ashgang/morphy/Software/ReferenceApplication/pca10056/s140/config/sdk_config.h

/**
 * Copyright (c) 2017 - 2020, Nordic Semiconductor ASA
 *
 * All rights reserved.
 *
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
 * 3. Neither the name of Nordic Semiconductor ASA nor the names of its
 *    contributors may be used to endorse or promote products derived from this
 *    software without specific prior written permission.
 *
 * 4. This software, with or without modification, must only be used with a
 *    Nordic Semiconductor ASA integrated circuit.
 *
 * 5. Any software provided in binary form under this license must not be reverse
 *    engineered, decompiled, modified and/or disassembled.
 *
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
 */



#ifndef SDK_CONFIG_H
#define SDK_CONFIG_H
// <<< Use Configuration Wizard in Context Menu >>>\n
#ifdef USE_APP_CONFIG
#include "app_config.h"
#endif
// <h> Board Support 

//==========================================================
// <q> BSP_BTN_BLE_ENABLED  - bsp_btn_ble - Button Control for BLE
 

#ifndef BSP_BTN_BLE_ENABLED
#define BSP_BTN_BLE_ENABLED 1
#endif

// </h> 
//==========================================================

// <h> nRF_BLE 

//==========================================================
// <q> BLE_ADVERTISING_ENABLED  - ble_advertising - Advertising module
 

#ifndef BLE_ADVERTISING_ENABLED
#define BLE_ADVERTISING_ENABLED 1
#endif

// <e> BLE_DTM_ENABLED - ble_dtm - Module for testing RF/PHY using DTM commands
//==========================================================
#ifndef BLE_DTM_ENABLED
#define BLE_DTM_ENABLED 0
#endif
// <o> NRF_RADIO_ANTENNA_PIN_1 - Antenna 1 GPIO pin 
#ifndef NRF_RADIO_ANTENNA_PIN_1
#define NRF_RADIO_ANTENNA_PIN_1 21
#endif

// <o> NRF_RADIO_ANTENNA_PIN_2 - Antenna 2 GPIO pin 
#ifndef NRF_RADIO_ANTENNA_PIN_2
#define NRF_RADIO_ANTENNA_PIN_2 23
#endif

// <o> NRF_RADIO_ANTENNA_PIN_3 - Antenna 3 GPIO pin 
#ifndef NRF_RADIO_ANTENNA_PIN_3
#define NRF_RADIO_ANTENNA_PIN_3 26
#endif

// <o> NRF_RADIO_ANTENNA_PIN_4 - Antenna 4 GPIO pin 
#ifndef NRF_RADIO_ANTENNA_PIN_4
#define NRF_RADIO_ANTENNA_PIN_4 27
#endif

// <o> NRF_RADIO_ANTENNA_PIN_5 - Antenna 5 GPIO pin 
#ifndef NRF_RADIO_ANTENNA_PIN_5
#define NRF_RADIO_ANTENNA_PIN_5 28
#endif

// <o> NRF_RADIO_ANTENNA_PIN_6 - Antenna 6 GPIO pin 
#ifndef NRF_RADIO_ANTENNA_PIN_6
#define NRF_RADIO_ANTENNA_PIN_6 29
#endif

// <o> NRF_RADIO_ANTENNA_PIN_7 - Antenna 7 GPIO pin 
#ifndef NRF_RADIO_ANTENNA_PIN_7
#define NRF_RADIO_ANTENNA_PIN_7 30
#endif

// <o> NRF_RADIO_ANTENNA_PIN_8 - Antenna 8 GPIO pin 
#ifndef NRF_RADIO_ANTENNA_PIN_8
#define NRF_RADIO_ANTENNA_PIN_8 31
#endif

// <o> NRF_RADIO_ANTENNA_COUNT  
#ifndef NRF_RADIO_ANTENNA_COUNT
#define NRF_RADIO_ANTENNA_COUNT 12
#endif

// </e>

// <q> BLE_RACP_ENABLED  - ble_racp - Record Access Control Point library
 

#ifndef BLE_RACP_ENABLED
#define BLE_RACP_ENABLED 0
#endif

// <e> NRF_BLE_CONN_PARAMS_ENABLED - ble_conn_params - Initiating and executing a connection parameters negotiation procedure
//==========================================================
#ifndef NRF_BLE_CONN_PARAMS_ENABLED
#define NRF_BLE_CONN_PARAMS_ENABLED 1
#endif
// <o> NRF_BLE_CONN_PARAMS_MAX_SLAVE_LATENCY_DEVIATION - The largest acceptable deviation in slave latency. 
// <i> The largest deviation (+ or -) from the requested slave latency that will not be renegotiated.

#ifndef NRF_BLE_CONN_PARAMS_MAX_SLAVE_LATENCY_DEVIATION
#define NRF_BLE_CONN_PARAMS_MAX_SLAVE_LATENCY_DEVIATION 499
#endif

// <o> NRF_BLE_CONN_PARAMS_MAX_SUPERVISION_TIMEOUT_DEVIATION - The largest acceptable deviation (in 10 ms units) in supervision timeout. 
// <i> The largest deviation (+ or -, in 10 ms units) from the requested supervision timeout that will not be renegotiated.

#ifndef NRF_BLE_CONN_PARAMS_MAX_SUPERVISION_TIMEOUT_DEVIATION
#define NRF_BLE_CONN_PARAMS_MAX_SUPERVISION_TIMEOUT_DEVIATION 65535
#endif

// </e>

// <q> NRF_BLE_GATT_ENABLED  - nrf_ble_gatt - GATT module
 

#ifndef NRF_BLE_GATT_ENABLED
#define NRF_BLE_GATT_ENABLED 1
#endif

// <e> NRF_BLE_QWR_ENABLED - nrf_ble_qwr - Queued writes support module (prepare/execute write)
//==========================================================
#ifndef NRF_BLE_QWR_ENABLED
#define NRF_BLE_QWR_ENABLED 1
#endif
// <o> NRF_BLE_QWR_MAX_ATTR - Maximum number of attribute handles that can be registered. This number must be adjusted according to the number of attributes for which Queued Writes will be enabled. If it is zero, the module will reject all Queued Write requests. 
#ifndef NRF_BLE_QWR_MAX_ATTR
#define NRF_BLE_QWR_MAX_ATTR 0
#endif

// </e>

// <e> PEER_MANAGER_ENABLED - peer_manager - Peer Manager
//==========================================================
#ifndef PEER_MANAGER_ENABLED
#define PEER_MANAGER_ENABLED 1
#endif
// <o> PM_MAX_REGISTRANTS - Number of event handlers that can be registered. 
#ifndef PM_MAX_REGISTRANTS
#define PM_MAX_REGISTRANTS 3
#endif

// <o> PM_FLASH_BUFFERS - Number of internal buffers for flash operations. 
// <i> Decrease this value to lower RAM usage.

#ifndef PM_FLASH_BUFFERS
#define PM_FLASH_BUFFERS 4
#endif

// <q> PM_CENTRAL_ENABLED  - Enable/disable central-specific Peer Manager functionality.
 

// <i> Enable/disable central-specific Peer Manager functionality.

#ifndef PM_CENTRAL_ENABLED
#define PM_CENTRAL_ENABLED 0
#endif

// <q> PM_SERVICE_CHANGED_ENABLED  - Enable/disable the service changed management for GATT server in Peer Manager.
 

// <i> If not using a GATT server, or using a server wihout a service changed characteristic,
// <i> disable this to save code space.

#ifndef PM_SERVICE_CHANGED_ENABLED
#define PM_SERVICE_CHANGED_ENABLED 1
#endif

// <q> PM_PEER_RANKS_ENABLED  - Enable/disable the peer rank management in Peer Manager.
 

// <i> Set this to false to save code space if not using the peer rank API.

#ifndef PM_PEER_RANKS_ENABLED
#define PM_PEER_RANKS_ENABLED 1
#endif

// <q> PM_LESC_ENABLED  - Enable/disable LESC support in Peer Manager.
 

// <i> If set to true, you need to call nrf_ble_lesc_request_handler() in the main loop to respond to LESC-related BLE events. If LESC support is not required, set this to false to save code space.

#ifndef PM_LESC_ENABLED
#define PM_LESC_ENABLED 0
#endif

// <e> PM_RA_PROTECTION_ENABLED - Enable/disable protection against repeated pairing attempts in Peer Manager.
//==========================================================
#ifndef PM_RA_PROTECTION_ENABLED
#define PM_RA_PROTECTION_ENABLED 0
#endif
// <o> PM_RA_PROTECTION_TRACKED_PEERS_NUM - Maximum number of peers whose authorization status can be tracked. 
#ifndef PM_RA_PROTECTION_TRACKED_PEERS_NUM
#define PM_RA_PROTECTION_TRACKED_PEERS_NUM 8
#endif

// <o> PM_RA_PROTECTION_MIN_WAIT_INTERVAL - Minimum waiting interval (in ms) before a new pairing attempt can be initiated. 
#ifndef PM_RA_PROTECTION_MIN_WAIT_INTERVAL
#define PM_RA_PROTECTION_MIN_WAIT_INTERVAL 4000
#endif

// <o> PM_RA_PROTECTION_MAX_WAIT_INTERVAL - Maximum waiting interval (in ms) before a new pairing attempt can be initiated. 
#ifndef PM_RA_PROTECTION_MAX_WAIT_INTERVAL
#define PM_RA_PROTECTION_MAX_WAIT_INTERVAL 64000
#endif

// <o> PM_RA_PROTECTION_REWARD_PERIOD - Reward period (in ms). 
// <i> The waiting interval is gradually decreased when no new failed pairing attempts are made during reward period.

#ifndef PM_RA_PROTECTION_REWARD_PERIOD
#define PM_RA_PROTECTION_REWARD_PERIOD 10000
#endif

// </e>

// <o> PM_HANDLER_SEC_DELAY_MS - Delay before starting security. 
// <i>  This might be necessary for interoperability reasons, especially as peripheral.

#ifndef PM_HANDLER_SEC_DELAY_MS
#define PM_HANDLER_SEC_DELAY_MS 0
#endif

// </e>

// </h> 
//==========================================================

// <h> nRF_BLE_Services 

//==========================================================
// <q> BLE_ANCS_C_ENABLED  - ble_ancs_c - Apple Notification Service Client
 

#ifndef BLE_ANCS_C_ENABLED
#define BLE_ANCS_C_ENABLED 0
#endif

// <q> BLE_ANS_C_ENABLED  - ble_ans_c - Alert Notification Service Client
 

#ifndef BLE_ANS_C_ENABLED
#define BLE_ANS_C_ENABLED 0
#endif

// <q> BLE_BAS_C_ENABLED  - ble_bas_c - Battery Service Client
 

#ifndef BLE_BAS_C_ENABLED
#define BLE_BAS_C_ENABLED 0
#endif

// <e> BLE_BAS_ENABLED - ble_bas - Battery Service
//==========================================================
#ifndef BLE_BAS_ENABLED
#define BLE_BAS_ENABLED 1
#endif
// <e> BLE_BAS_CONFIG_LOG_ENABLED - Enables logging in the module.
//==========================================================
#ifndef BLE_BAS_CONFIG_LOG_ENABLED
#define BLE_BAS_CONFIG_LOG_ENABLED 0
#endif
// <o> BLE_BAS_CONFIG_LOG_LEVEL  - Default Severity level
 
// <0=> Off 
// <1=> Error 
// <2=> Warning 
// <3=> Info 
// <4=> Debug 

#ifndef BLE_BAS_CONFIG_LOG_LEVEL
#define BLE_BAS_CONFIG_LOG_LEVEL 3
#endif

// <o> BLE_BAS_CONFIG_INFO_COLOR  - ANSI escape code prefix.
 
// <0=> Default 
// <1=> Black 
// <2=> Red 
// <3=> Green 
// <4=> Yellow 
// <5=> Blue 
// <6=> Magenta 
// <7=> Cyan 
// <8=> White 

#ifndef BLE_BAS_CONFIG_INFO_COLOR
#define BLE_BAS_CONFIG_INFO_COLOR 0
#endif

// <o> BLE_BAS_CONFIG_DEBUG_COLOR  - ANSI escape code prefix.
 
// <0=> Default 
// <1=> Black 
// <2=> Red 
// <3=> Green 
// <4=> Yellow 
// <5=> Blue 
// <6=> Magenta 
// <7=> Cyan 
// <8=> White 

#ifndef BLE_BAS_CONFIG_DEBUG_COLOR
#define BLE_BAS_CONFIG_DEBUG_COLOR 0
#endif

// </e>

// </e>

// <q> BLE_CSCS_ENABLED  - ble_cscs - Cycling Speed and Cadence Service
 

#ifndef BLE_CSCS_ENABLED
#define BLE_CSCS_ENABLED 0
#endif

// <q> BLE_CTS_C_ENABLED  - ble_cts_c - Current Time Service Client
 

#ifndef BLE_CTS_C_ENABLED
#define BLE_CTS_C_ENABLED 0
#endif

// <q> BLE_DIS_ENABLED  - ble_dis - Device Information Service
 

#ifndef BLE_DIS_ENABLED
#define BLE_DIS_ENABLED 1
#endif

// <q> BLE_GLS_ENABLED  - ble_gls - Glucose Service
 

#ifndef BLE_GLS_ENABLED
#define BLE_GLS_ENABLED 0
#endif

// <q> BLE_HIDS_ENABLED  - ble_hids - Human Interface Device Service
 

#ifndef BLE_HIDS_ENABLED
#define BLE_HIDS_ENABLED 0
#endif

// <q> BLE_HRS_C_ENABLED  - ble_hrs_c - Heart Rate Service Client
 

#ifndef BLE_HRS_C_ENABLED
#define BLE_HRS_C_ENABLED 0
#endif

// <q> BLE_HRS_ENABLED  - ble_hrs - Heart Rate Service
 

#ifndef BLE_HRS_ENABLED
#define BLE_HRS_ENABLED 1
#endif

// <q> BLE_HTS_ENABLED  - ble_hts - Health Thermometer Service
 

#ifndef BLE_HTS_ENABLED
#define BLE_HTS_ENABLED 0
#endif

// <q> BLE_IAS_C_ENABLED  - ble_ias_c - Immediate Alert Service Client
 

#ifndef BLE_IAS_C_ENABLED
#define BLE_IAS_C_ENABLED 0
#endif

// <e> BLE_IAS_ENABLED - ble_ias - Immediate Alert Service
//==========================================================
#ifndef BLE_IAS_ENABLED
#define BLE_IAS_ENABLED 0
#endif
// <e> BLE_IAS_CONFIG_LOG_ENABLED - Enables logging in the module.
//==========================================================
#ifndef BLE_IAS_CONFIG_LOG_ENABLED
#define BLE_IAS_CONFIG_LOG_ENABLED 0
#endif
// <o> BLE_IAS_CONFIG_LOG_LEVEL  - Default Severity level
 
// <0=> Off 
// <1=> Error 
// <2=> Warning 
// <3=> Info 
// <4=> Debug 

#ifndef BLE_IAS_CONFIG_LOG_LEVEL
#define BLE_IAS_CONFIG_LOG_LEVEL 3
#endif

// <o> BLE_IAS_CONFIG_INFO_COLOR  - ANSI escape code prefix.
 
// <0=> Default 
// <1=> Black 
// <2=> Red 
// <3=> Green 
// <4=> Yellow 
// <5=> Blue 
// <6=> Magenta 
// <7=> Cyan 
// <8=> White 

#ifndef BLE_IAS_CONFIG_INFO_COLOR
#define BLE_IAS_CONFIG_INFO_COLOR 0
#endif

// <o> BLE_IAS_CONFIG_DEBUG_COLOR  - ANSI escape code prefix.
 
// <0=> Default 
// <1=> Black 
// <2=> Red 
// <3=> Green 
// <4=> Yellow 
// <5=> Blue 
// <6=> Magenta 
// <7=> Cyan 
// <8=> White 

#ifndef BLE_IAS_CONFIG_DEBUG_COLOR
#define BLE_IAS_CONFIG_DEBUG_COLOR 0
#endif

// </e>

// </e>

// <q> BLE_LBS_C_ENABLED  - ble_lbs_c - Nordic LED Button Service Client
 

#ifndef BLE_LBS_C_ENABLED
#define BLE_LBS_C_ENABLED 0
#endif

// <q> BLE_LBS_ENABLED  - ble_lbs - LED Button Service
 

#ifndef BLE_LBS_ENABLED
#define BLE_LBS_ENABLED 0
#endif

// <q> BLE_LLS_ENABLED  - ble_lls - Link Loss Service
 

#ifndef BLE_LLS_ENABLED
#define BLE_LLS_ENABLED 0
#endif

// <q> BLE_NUS_C_ENABLED  - ble_nus_c - Nordic UART Central Service
 

#ifndef BLE_NUS_C_ENABLED
#define BLE_NUS_C_ENABLED 0
#endif

// <e> BLE_NUS_ENABLED - ble_nus - Nordic UART Service
//==========================================================
#ifndef BLE_NUS_ENABLED
#define BLE_NUS_ENABLED 0
#endif
// <e> BLE_NUS_CONFIG_LOG_ENABLED - Enables logging in the module.
//==========================================================
#ifndef BLE_NUS_CONFIG_LOG_ENABLED
#define BLE_NUS_CONFIG_LOG_ENABLED 0
#endif
// <o> BLE_NUS_CONFIG_LOG_LEVEL  - Default Severity level
 
// <0=> Off 
// <1=> Error 
// <2=> Warning 
// <3=> Info 
// <4=> Debug 

#ifndef BLE_NUS_CONFIG_LOG_LEVEL
#define BLE_NUS_CONFIG_LOG_LEVEL 3
#endif

// <o> BLE_NUS_CONFIG_INFO_COLOR  - ANSI escape code prefix.
 
// <0=> Default 
// <1=> Black 
// <2=> Red 
// <3=> Green 
// <4=> Yellow 
// <5=> Blue 
// <6=> Magenta 
// <7=> Cyan 
// <8=> White 

#ifndef BLE_NUS_CONFIG_INFO_COLOR
#define BLE_NUS_CONFIG_INFO_COLOR 0
#endif

// <o> BLE_NUS_CONFIG_DEBUG_COLOR  - ANSI escape code prefix.
 
// <0=> Default 
// <1=> Black 
// <2=> Red 
// <3=> Green 
// <4=> Yellow 
// <5=> Blue 
// <6=> Magenta 
// <7=> Cyan 
// <8=> White 

#ifndef BLE_NUS_CONFIG_DEBUG_COLOR
#define BLE_NUS_CONFIG_DEBUG_COLOR 0
#endif

// </e>

// </e>

// <q> BLE_RSCS_C_ENABLED  - ble_rscs_c - Running Speed and Cadence Client
 

#ifndef BLE_RSCS_C_ENABLED
#define BLE_RSCS_C_ENABLED 0
#endif

// <q> BLE_RSCS_ENABLED  - ble_rscs - Running Speed and Cadence Service
 

#ifndef BLE_RSCS_ENABLED
#define BLE_RSCS_ENABLED 0
#endif

// <q> BLE_TPS_ENABLED  - ble_tps - TX Power Service
 

#ifndef BLE_TPS_ENABLED
#define BLE_TPS_ENABLED 0
#endif

// </h> 
//==========================================================

// <h> nRF_Core 

//==========================================================
// <e> NRF_MPU_LIB_ENABLED - nrf_mpu_lib - Module for MPU
//==========================================================
#ifndef NRF_MPU_LIB_ENABLED
#define NRF_MPU_LIB_ENABLED 0
#endif
// <q> NRF_MPU_LIB_CLI_CMDS  - Enable CLI commands specific to the module.
 

#ifndef NRF_MPU_LIB_CLI_CMDS
#define NRF_MPU_LIB_CLI_CMDS 0
#endif

// </e>

// <e> NRF_STACK_GUARD_ENABLED - nrf_stack_guard - Stack guard
//==========================================================
#ifndef NRF_STACK_GUARD_ENABLED
#define NRF_STACK_GUARD_ENABLED 0
#endif
// <o> NRF_STACK_GUARD_CONFIG_SIZE  - Size of the stack guard.
 
// <5=> 32 bytes 
// <6=> 64 bytes 
// <7=> 128 bytes 
// <8=> 256 bytes 
// <9=> 512 bytes 
// <10=> 1024 bytes 
// <11=> 2048 bytes 
// <12=> 4096 bytes 

#ifndef NRF_STACK_GUARD_CONFIG_SIZE
#define NRF_STACK_GUARD_CONFIG_SIZE 7
#endif

// </e>

// </h> 
//==========================================================

// <h> nRF_Crypto 

//==========================================================
// <e> NRF_CRYPTO_ENABLED - nrf_crypto - Cryptography library.
//==========================================================
#ifndef NRF_CRYPTO_ENABLED
#define NRF_CRYPTO_ENABLED 1
#endif
// <o> NRF_CRYPTO_ALLOCATOR  - Memory allocator
 

// <i> Choose memory allocator used by nrf_crypto. Default is alloca if possible or nrf_malloc otherwise. If 'User macros' are selected, the user has to create 'nrf_crypto_allocator.h' file that contains NRF_CRYPTO_ALLOC, NRF_CRYPTO_FREE, and NRF_CRYPTO_ALLOC_ON_STACK.
// <0=> Default 
// <1=> User macros 
// <2=> On stack (alloca) 
// <3=> C dynamic memory (malloc) 
// <4=> SDK Memory Manager (nrf_malloc) 

#ifndef NRF_CRYPTO_ALLOCATOR
#define NRF_CRYPTO_ALLOCATOR 0
#endif

// <e> NRF_CRYPTO_BACKEND_CC310_BL_ENABLED - Enable the ARM Cryptocell CC310 reduced backend.

// <i> The CC310 hardware-accelerated cryptography backend with reduced functionality and footprint (only available on nRF52840).
//==========================================================
#ifndef NRF_CRYPTO_BACKEND_CC310_BL_ENABLED
#define NRF_CRYPTO_BACKEND_CC310_BL_ENABLED 0
#endif
// <q> NRF_CRYPTO_BACKEND_CC310_BL_ECC_SECP224R1_ENABLED  - Enable the secp224r1 elliptic curve support using CC310_BL.
 

#ifndef NRF_CRYPTO_BACKEND_CC310_BL_ECC_SECP224R1_ENABLED
#define NRF_CRYPTO_BACKEND_CC310_BL_ECC_SECP224R1_ENABLED 0
#endif

// <q> NRF_CRYPTO_BACKEND_CC310_BL_ECC_SECP256R1_ENABLED  - Enable the secp256r1 elliptic curve support using CC310_BL.
 

#ifndef NRF_CRYPTO_BACKEND_CC310_BL_ECC_SECP256R1_ENABLED
#define NRF_CRYPTO_BACKEND_CC310_BL_ECC_SECP256R1_ENABLED 1
#endif

// <q> NRF_CRYPTO_BACKEND_CC310_BL_HASH_SHA256_ENABLED  - CC310_BL SHA-256 hash functionality.
 

// <i> CC310_BL backend implementation for hardware-accelerated SHA-256.

#ifndef NRF_CRYPTO_BACKEND_CC310_BL_HASH_SHA256_ENABLED
#define NRF_CRYPTO_BACKEND_CC310_BL_HASH_SHA256_ENABLED 1
#endif

// <q> NRF_CRYPTO_BACKEND_CC310_BL_HASH_AUTOMATIC_RAM_BUFFER_ENABLED  - nrf_cc310_bl buffers to RAM before running hash operation
 

// <i> Enabling this makes hashing of addresses in FLASH range possible. Size of buffer allocated for hashing is set by NRF_CRYPTO_BACKEND_CC310_BL_HASH_AUTOMATIC_RAM_BUFFER_SIZE

#ifndef NRF_CRYPTO_BACKEND_CC310_BL_HASH_AUTOMATIC_RAM_BUFFER_ENABLED
#define NRF_CRYPTO_BACKEND_CC310_BL_HASH_AUTOMATIC_RAM_BUFFER_ENABLED 0
#endif

// <o> NRF_CRYPTO_BACKEND_CC310_BL_HASH_AUTOMATIC_RAM_BUFFER_SIZE - nrf_cc310_bl hash outputs digests in little endian 
// <i> Makes the nrf_cc310_bl hash functions output digests in little endian format. Only for use in nRF SDK DFU!

#ifndef NRF_CRYPTO_BACKEND_CC310_BL_HASH_AUTOMATIC_RAM_BUFFER_SIZE
#define NRF_CRYPTO_BACKEND_CC310_BL_HASH_AUTOMATIC_RAM_BUFFER_SIZE 4096
#endif

// <q> NRF_CRYPTO_BACKEND_CC310_BL_INTERRUPTS_ENABLED  - Enable Interrupts while support using CC310 bl.
 

// <i> Select a library version compatible with the configuration. When interrupts are disable, a version named _noint must be used

#ifndef NRF_CRYPTO_BACKEND_CC310_BL_INTERRUPTS_ENABLED
#define NRF_CRYPTO_BACKEND_CC310_BL_INTERRUPTS_ENABLED 1
#endif

// </e>

// <e> NRF_CRYPTO_BACKEND_CC310_ENABLED - Enable the ARM Cryptocell CC310 backend.

// <i> The CC310 hardware-accelerated cryptography backend (only available on nRF52840).
//==========================================================
#ifndef NRF_CRYPTO_BACKEND_CC310_ENABLED
#define NRF_CRYPTO_BACKEND_CC310_ENABLED 0
#endif
// <q> NRF_CRYPTO_BACKEND_CC310_AES_CBC_ENABLED  - Enable the AES CBC mode using CC310.
 

#ifndef NRF_CRYPTO_BACKEND_CC310_AES_CBC_ENABLED
#define NRF_CRYPTO_BACKEND_CC310_AES_CBC_ENABLED 1
#endif

// <q> NRF_CRYPTO_BACKEND_CC310_AES_CTR_ENABLED  - Enable the AES CTR mode using CC310.
 

#ifndef NRF_CRYPTO_BACKEND_CC310_AES_CTR_ENABLED
#define NRF_CRYPTO_BACKEND_CC310_AES_CTR_ENABLED 1
#endif

// <q> NRF_CRYPTO_BACKEND_CC310_AES_ECB_ENABLED  - Enable the AES ECB mode using CC310.
 

#ifndef NRF_CRYPTO_BACKEND_CC310_AES_ECB_ENABLED
#define NRF_CRYPTO_BACKEND_CC310_AES_ECB_ENABLED 1
#endif

// <q> NRF_CRYPTO_BACKEND_CC310_AES_CBC_MAC_ENABLED  - Enable the AES CBC_MAC mode using CC310.
 

#ifndef NRF_CRYPTO_BACKEND_CC310_AES_CBC_MAC_ENABLED
#define NRF_CRYPTO_BACKEND_CC310_AES_CBC_MAC_ENABLED 1
#endif

// <q> NRF_CRYPTO_BACKEND_CC310_AES_CMAC_ENABLED  - Enable the AES CMAC mode using CC310.
 

#ifndef NRF_CRYPTO_BACKEND_CC310_AES_CMAC_ENABLED
#define NRF_CRYPTO_BACKEND_CC310_AES_CMAC_ENABLED 1
#endif

// <q> NRF_CRYPTO_BACKEND_CC310_AES_CCM_ENABLED  - Enable the AES CCM mode using CC310.
 

#ifndef NRF_CRYPTO_BACKEND_CC310_AES_CCM_ENABLED
#define NRF_CRYPTO_BACKEND_CC310_AES_CCM_ENABLED 1
#endif

// <q> NRF_CRYPTO_BACKEND_CC310_AES_CCM_STAR_ENABLED  - Enable the AES CCM* mode using CC310.
 

#ifndef NRF_CRYPTO_BACKEND_CC310_AES_CCM_STAR_ENABLED
#define NRF_CRYPTO_BACKEND_CC310_AES_CCM_STAR_ENABLED 1
#endif

// <q> NRF_CRYPTO_BACKEND_CC310_CHACHA_POLY_ENABLED  - Enable the CHACHA-POLY mode using CC310.
 

#ifndef NRF_CRYPTO_BACKEND_CC310_CHACHA_POLY_ENABLED
#define NRF_CRYPTO_BACKEND_CC310_CHACHA_POLY_ENABLED 1
#endif

// <q> NRF_CRYPTO_BACKEND_CC310_ECC_SECP160R1_ENABLED  - Enable the secp160r1 elliptic curve support using CC310.
 

#ifndef NRF_CRYPTO_BACKEND_CC310_ECC_SECP160R1_ENABLED
#define NRF_CRYPTO_BACKEND_CC310_ECC_SECP160R1_ENABLED 1
#endif

// <q> NRF_CRYPTO_BACKEND_CC310_ECC_SECP160R2_ENABLED  - Enable the secp160r2 elliptic curve support using CC310.
 

#ifndef NRF_CRYPTO_BACKEND_CC310_ECC_SECP160R2_ENABLED
#define NRF_CRYPTO_BACKEND_CC310_ECC_SECP160R2_ENABLED 1
#endif

// <q> NRF_CRYPTO_BACKEND_CC310_ECC_SECP192R1_ENABLED  - Enable the secp192r1 elliptic curve support using CC310.
 

#ifndef NRF_CRYPTO_BACKEND_CC310_ECC_SECP192R1_ENABLED
#define NRF_CRYPTO_BACKEND_CC310_ECC_SECP192R1_ENABLED 1
#endif

// <q> NRF_CRYPTO_BACKEND_CC310_ECC_SECP224R1_ENABLED  - Enable the secp224r1 elliptic curve support using CC310.
 

#ifndef NRF_CRYPTO_BACKEND_CC310_ECC_SECP224R1_ENABLED
#define NRF_CRYPTO_BACKEND_CC310_ECC_SECP224R1_ENABLED 1
#endif

// <q> NRF_CRYPTO_BACKEND_CC310_ECC_SECP256R1_ENABLED  - Enable the secp256r1 elliptic curve support using CC310.
 

#ifndef NRF_CRYPTO_BACKEND_CC310_ECC_SECP256R1_ENABLED
#define NRF_CRYPTO_BACKEND_CC310_ECC_SECP256R1_ENABLED 1
#endif

// <q> NRF_CRYPTO_BACKEND_CC310_ECC_SECP384R1_ENABLED  - Enable the secp384r1 elliptic curve support using CC310.
 

#ifndef NRF_CRYPTO_BACKEND_CC310_ECC_SECP384R1_ENABLED
#define NRF_CRYPTO_BACKEND_CC310_ECC_SECP384R1_ENABLED 1
#endif

// <q> NRF_CRYPTO_BACKEND_CC310_ECC_SECP521R1_ENABLED  - Enable the secp521r1 elliptic curve support using CC310.
 

#ifndef NRF_CRYPTO_BACKEND_CC310_ECC_SECP521R1_ENABLED
#define NRF_CRYPTO_BACKEND_CC310_ECC_SECP521R1_ENABLED 1
#endif

// <q> NRF_CRYPTO_BACKEND_CC310_ECC_SECP160K1_ENABLED  - Enable the secp160k1 elliptic curve support using CC310.
 

#ifndef NRF_CRYPTO_BACKEND_CC310_ECC_SECP160K1_ENABLED
#define NRF_CRYPTO_BACKEND_CC310_ECC_SECP160K1_ENABLED 1
#endif

// <q> NRF_CRYPTO_BACKEND_CC310_ECC_SECP192K1_ENABLED  - Enable the secp192k1 elliptic curve support using CC310.
 

#ifndef NRF_CRYPTO_BACKEND_CC310_ECC_SECP192K1_ENABLED
#define NRF_CRYPTO_BACKEND_CC310_ECC_SECP192K1_ENABLED 1
#endif

// <q> NRF_CRYPTO_BACKEND_CC310_ECC_SECP224K1_ENABLED  - Enable the secp224k1 elliptic curve support using CC310.
 

#ifndef NRF_CRYPTO_BACKEND_CC310_ECC_SECP224K1_ENABLED
#define NRF_CRYPTO_BACKEND_CC310_ECC_SECP224K1_ENABLED 1
#endif

// <q> NRF_CRYPTO_BACKEND_CC310_ECC_SECP256K1_ENABLED  - Enable the secp256k1 elliptic curve support using CC310.
 

#ifndef NRF_CRYPTO_BACKEND_CC310_ECC_SECP256K1_ENABLED
#define NRF_CRYPTO_BACKEND_CC310_ECC_SECP256K1_ENABLED 1
#endif

// <q> NRF_CRYPTO_BACKEND_CC310_ECC_CURVE25519_ENABLED  - Enable the Curve25519 curve support using CC310.
 

#ifndef NRF_CRYPTO_BACKEND_CC310_ECC_CURVE25519_ENABLED
#define NRF_CRYPTO_BACKEND_CC310_ECC_CURVE25519_ENABLED 1
#endif

// <q> NRF_CRYPTO_BACKEND_CC310_ECC_ED25519_ENABLED  - Enable the Ed25519 curve support using CC310.
 

#ifndef NRF_CRYPTO_BACKEND_CC310_ECC_ED25519_ENABLED
#define NRF_CRYPTO_BACKEND_CC310_ECC_ED25519_ENABLED 1
#endif

// <q> NRF_CRYPTO_BACKEND_CC310_HASH_SHA256_ENABLED  - CC310 SHA-256 hash functionality.
 

// <i> CC310 backend implementation for hardware-accelerated SHA-256.

#ifndef NRF_CRYPTO_BACKEND_CC310_HASH_SHA256_ENABLED
#define NRF_CRYPTO_BACKEND_CC310_HASH_SHA256_ENABLED 1
#endif

// <q> NRF_CRYPTO_BACKEND_CC310_HASH_SHA512_ENABLED  - CC310 SHA-512 hash functionality
 

// <i> CC310 backend implementation for SHA-512 (in software).

#ifndef NRF_CRYPTO_BACKEND_CC310_HASH_SHA512_ENABLED
#define NRF_CRYPTO_BACKEND_CC310_HASH_SHA512_ENABLED 1
#endif

// <q> NRF_CRYPTO_BACKEND_CC310_HMAC_SHA256_ENABLED  - CC310 HMAC using SHA-256
 

// <i> CC310 backend implementation for HMAC using hardware-accelerated SHA-256.

#ifndef NRF_CRYPTO_BACKEND_CC310_HMAC_SHA256_ENABLED
#define NRF_CRYPTO_BACKEND_CC310_HMAC_SHA256_ENABLED 1
#endif

// <q> NRF_CRYPTO_BACKEND_CC310_HMAC_SHA512_ENABLED  - CC310 HMAC using SHA-512
 

// <i> CC310 backend implementation for HMAC using SHA-512 (in software).

#ifndef NRF_CRYPTO_BACKEND_CC310_HMAC_SHA512_ENABLED
#define NRF_CRYPTO_BACKEND_CC310_HMAC_SHA512_ENABLED 1
#endif

// <q> NRF_CRYPTO_BACKEND_CC310_RNG_ENABLED  - Enable RNG support using CC310.
 

#ifndef NRF_CRYPTO_BACKEND_CC310_RNG_ENABLED
#define NRF_CRYPTO_BACKEND_CC310_RNG_ENABLED 1
#endif

// <q> NRF_CRYPTO_BACKEND_CC310_INTERRUPTS_ENABLED  - Enable Interrupts while support using CC310.
 

// <i> Select a library version compatible with the configuration. When interrupts are disable, a version named _noint must be used

#ifndef NRF_CRYPTO_BACKEND_CC310_INTERRUPTS_ENABLED
#define NRF_CRYPTO_BACKEND_CC310_INTERRUPTS_ENABLED 1
#endif

// </e>

// <e> NRF_CRYPTO_BACKEND_CIFRA_ENABLED - Enable the Cifra backend.
//==========================================================
#ifndef NRF_CRYPTO_BACKEND_CIFRA_ENABLED
#define NRF_CRYPTO_BACKEND_CIFRA_ENABLED 0
#endif
// <q> NRF_CRYPTO_BACKEND_CIFRA_AES_EAX_ENABLED  - Enable the AES EAX mode using Cifra.
 

#ifndef NRF_CRYPTO_BACKEND_CIFRA_AES_EAX_ENABLED
#define NRF_CRYPTO_BACKEND_CIFRA_AES_EAX_ENABLED 1
#endif

// </e>

// <e> NRF_CRYPTO_BACKEND_MBEDTLS_ENABLED - Enable the mbed TLS backend.
//==========================================================
#ifndef NRF_CRYPTO_BACKEND_MBEDTLS_ENABLED
#define NRF_CRYPTO_BACKEND_MBEDTLS_ENABLED 0
#endif
// <q> NRF_CRYPTO_BACKEND_MBEDTLS_AES_CBC_ENABLED  - Enable the AES CBC mode mbed TLS.
 

#ifndef NRF_CRYPTO_BACKEND_MBEDTLS_AES_CBC_ENABLED
#define NRF_CRYPTO_BACKEND_MBEDTLS_AES_CBC_ENABLED 1
#endif

// <q> NRF_CRYPTO_BACKEND_MBEDTLS_AES_CTR_ENABLED  - Enable the AES CTR mode using mbed TLS.
 

#ifndef NRF_CRYPTO_BACKEND_MBEDTLS_AES_CTR_ENABLED
#define NRF_CRYPTO_BACKEND_MBEDTLS_AES_CTR_ENABLED 1
#endif

// <q> NRF_CRYPTO_BACKEND_MBEDTLS_AES_CFB_ENABLED  - Enable the AES CFB mode using mbed TLS.
 

#ifndef NRF_CRYPTO_BACKEND_MBEDTLS_AES_CFB_ENABLED
#define NRF_CRYPTO_BACKEND_MBEDTLS_AES_CFB_ENABLED 1
#endif

// <q> NRF_CRYPTO_BACKEND_MBEDTLS_AES_ECB_ENABLED  - Enable the AES ECB mode using mbed TLS.
 

#ifndef NRF_CRYPTO_BACKEND_MBEDTLS_AES_ECB_ENABLED
#define NRF_CRYPTO_BACKEND_MBEDTLS_AES_ECB_ENABLED 1
#endif

// <q> NRF_CRYPTO_BACKEND_MBEDTLS_AES_CBC_MAC_ENABLED  - Enable the AES CBC MAC mode using mbed TLS.
 

#ifndef NRF_CRYPTO_BACKEND_MBEDTLS_AES_CBC_MAC_ENABLED
#define NRF_CRYPTO_BACKEND_MBEDTLS_AES_CBC_MAC_ENABLED 1
#endif

// <q> NRF_CRYPTO_BACKEND_MBEDTLS_AES_CMAC_ENABLED  - Enable the AES CMAC mode using mbed TLS.
 

#ifndef NRF_CRYPTO_BACKEND_MBEDTLS_AES_CMAC_ENABLED
#define NRF_CRYPTO_BACKEND_MBEDTLS_AES_CMAC_ENABLED 1
#endif

// <q> NRF_CRYPTO_BACKEND_MBEDTLS_AES_CCM_ENABLED  - Enable the AES CCM mode using mbed TLS.
 

#ifndef NRF_CRYPTO_BACKEND_MBEDTLS_AES_CCM_ENABLED
#define NRF_CRYPTO_BACKEND_MBEDTLS_AES_CCM_ENABLED 1
#endif

// <q> NRF_CRYPTO_BACKEND_MBEDTLS_AES_GCM_ENABLED  - Enable the AES GCM mode using mbed TLS.
 

#ifndef NRF_CRYPTO_BACKEND_MBEDTLS_AES_GCM_ENABLED
#define NRF_CRYPTO_BACKEND_MBEDTLS_AES_GCM_ENABLED 1
#endif

// <q> NRF_CRYPTO_BACKEND_MBEDTLS_ECC_SECP192R1_ENABLED  - Enable secp192r1 (NIST 192-bit) curve
 

// <i> Enable this setting if you need secp192r1 (NIST 192-bit) support using MBEDTLS

#ifndef NRF_CRYPTO_BACKEND_MBEDTLS_ECC_SECP192R1_ENABLED
#define NRF_CRYPTO_BACKEND_MBEDTLS_ECC_SECP192R1_ENABLED 1
#endif

// <q> NRF_CRYPTO_BACKEND_MBEDTLS_ECC_SECP224R1_ENABLED  - Enable secp224r1 (NIST 224-bit) curve
 

// <i> Enable this setting if you need secp224r1 (NIST 224-bit) support using MBEDTLS

#ifndef NRF_CRYPTO_BACKEND_MBEDTLS_ECC_SECP224R1_ENABLED
#define NRF_CRYPTO_BACKEND_MBEDTLS_ECC_SECP224R1_ENABLED 1
#endif

// <q> NRF_CRYPTO_BACKEND_MBEDTLS_ECC_SECP256R1_ENABLED  - Enable secp256r1 (NIST 256-bit) curve
 

// <i> Enable this setting if you need secp256r1 (NIST 256-bit) support using MBEDTLS

#ifndef NRF_CRYPTO_BACKEND_MBEDTLS_ECC_SECP256R1_ENABLED
#define NRF_CRYPTO_BACKEND_MBEDTLS_ECC_SECP256R1_ENABLED 1
#endif

// <q> NRF_CRYPTO_BACKEND_MBEDTLS_ECC_SECP384R1_ENABLED  - Enable secp384r1 (NIST 384-bit) curve
 

// <i> Enable this setting if you need secp384r1 (NIST 384-bit) support using MBEDTLS

#ifndef NRF_CRYPTO_BACKEND_MBEDTLS_ECC_SECP384R1_ENABLED
#define NRF_CRYPTO_BACKEND_MBEDTLS_ECC_SECP384R1_ENABLED 1
#endif

// <q> NRF_CRYPTO_BACKEND_MBEDTLS_ECC_SECP521R1_ENABLED  - Enable secp521r1 (NIST 521-bit) curve
 

// <i> Enable this setting if you need secp521r1 (NIST 521-bit) support using MBEDTLS

#ifndef NRF_CRYPTO_BACKEND_MBEDTLS_ECC_SECP521R1_ENABLED
#define NRF_CRYPTO_BACKEND_MBEDTLS_ECC_SECP521R1_ENABLED 1
#endif

// <q> NRF_CRYPTO_BACKEND_MBEDTLS_ECC_SECP192K1_ENABLED  - Enable secp192k1 (Koblitz 192-bit) curve
 

// <i> Enable this setting if you need secp192k1 (Koblitz 192-bit) support using MBEDTLS

#ifndef NRF_CRYPTO_BACKEND_MBEDTLS_ECC_SECP192K1_ENABLED
#define NRF_CRYPTO_BACKEND_MBEDTLS_ECC_SECP192K1_ENABLED 1
#endif

// <q> NRF_CRYPTO_BACKEND_MBEDTLS_ECC_SECP224K1_ENABLED  - Enable secp224k1 (Koblitz 224-bit) curve
 

// <i> Enable this setting if you need secp224k1 (Koblitz 224-bit) support using MBEDTLS

#ifndef NRF_CRYPTO_BACKEND_MBEDTLS_ECC_SECP224K1_ENABLED
#define NRF_CRYPTO_BACKEND_MBEDTLS_ECC_SECP224K1_ENABLED 1
#endif

// <q> NRF_CRYPTO_BACKEND_MBEDTLS_ECC_SECP256K1_ENABLED  - Enable secp256k1 (Koblitz 256-bit) curve
 

// <i> Enable this setting if you need secp256k1 (Koblitz 256-bit) support using MBEDTLS

#ifndef NRF_CRYPTO_BACKEND_MBEDTLS_ECC_SECP256K1_ENABLED
#define NRF_CRYPTO_BACKEND_MBEDTLS_ECC_SECP256K1_ENABLED 1
#endif

// <q> NRF_CRYPTO_BACKEND_MBEDTLS_ECC_BP256R1_ENABLED  - Enable bp256r1 (Brainpool 256-bit) curve
 

// <i> Enable this setting if you need bp256r1 (Brainpool 256-bit) support using MBEDTLS

#ifndef NRF_CRYPTO_BACKEND_MBEDTLS_ECC_BP256R1_ENABLED
#define NRF_CRYPTO_BACKEND_MBEDTLS_ECC_BP256R1_ENABLED 1
#endif

// <q> NRF_CRYPTO_BACKEND_MBEDTLS_ECC_BP384R1_ENABLED  - Enable bp384r1 (Brainpool 384-bit) curve
 

// <i> Enable this setting if you need bp384r1 (Brainpool 384-bit) support using MBEDTLS

#ifndef NRF_CRYPTO_BACKEND_MBEDTLS_ECC_BP384R1_ENABLED
#define NRF_CRYPTO_BACKEND_MBEDTLS_ECC_BP384R1_ENABLED 1
#endif

// <q> NRF_CRYPTO_BACKEND_MBEDTLS_ECC_BP512R1_ENABLED  - Enable bp512r1 (Brainpool 512-bit) curve
 

// <i> Enable this setting if you need bp512r1 (Brainpool 512-bit) support using MBEDTLS

#ifndef NRF_CRYPTO_BACKEND_MBEDTLS_ECC_BP512R1_ENABLED
#define NRF_CRYPTO_BACKEND_MBEDTLS_ECC_BP512R1_ENABLED 1
#endif

// <q> NRF_CRYPTO_BACKEND_MBEDTLS_ECC_CURVE25519_ENABLED  - Enable Curve25519 curve
 

// <i> Enable this setting if you need Curve25519 support using MBEDTLS

#ifndef NRF_CRYPTO_BACKEND_MBEDTLS_ECC_CURVE25519_ENABLED
#define NRF_CRYPTO_BACKEND_MBEDTLS_ECC_CURVE25519_ENABLED 1
#endif

// <q> NRF_CRYPTO_BACKEND_MBEDTLS_HASH_SHA256_ENABLED  - Enable mbed TLS SHA-256 hash functionality.
 

// <i> mbed TLS backend implementation for SHA-256.

#ifndef NRF_CRYPTO_BACKEND_MBEDTLS_HASH_SHA256_ENABLED
#define NRF_CRYPTO_BACKEND_MBEDTLS_HASH_SHA256_ENABLED 1
#endif

// <q> NRF_CRYPTO_BACKEND_MBEDTLS_HASH_SHA512_ENABLED  - Enable mbed TLS SHA-512 hash functionality.
 

// <i> mbed TLS backend implementation for SHA-512.

#ifndef NRF_CRYPTO_BACKEND_MBEDTLS_HASH_SHA512_ENABLED
#define NRF_CRYPTO_BACKEND_MBEDTLS_HASH_SHA512_ENABLED 1
#endif

// <q> NRF_CRYPTO_BACKEND_MBEDTLS_HMAC_SHA256_ENABLED  - Enable mbed TLS HMAC using SHA-256.
 

// <i> mbed TLS backend implementation for HMAC using SHA-256.

#ifndef NRF_CRYPTO_BACKEND_MBEDTLS_HMAC_SHA256_ENABLED
#define NRF_CRYPTO_BACKEND_MBEDTLS_HMAC_SHA256_ENABLED 1
#endif

// <q> NRF_CRYPTO_BACKEND_MBEDTLS_HMAC_SHA512_ENABLED  - Enable mbed TLS HMAC using SHA-512.
 

// <i> mbed TLS backend implementation for HMAC using SHA-512.

#ifndef NRF_CRYPTO_BACKEND_MBEDTLS_HMAC_SHA512_ENABLED
#define NRF_CRYPTO_BACKEND_MBEDTLS_HMAC_SHA512_ENABLED 1
#endif

// </e>

// <e> NRF_CRYPTO_BACKEND_MICRO_ECC_ENABLED - Enable the micro-ecc backend.
//==========================================================
#ifndef NRF_CRYPTO_BACKEND_MICRO_ECC_ENABLED
#define NRF_CRYPTO_BACKEND_MICRO_ECC_ENABLED 0
#endif
// <q> NRF_CRYPTO_BACKEND_MICRO_ECC_ECC_SECP192R1_ENABLED  - Enable secp192r1 (NIST 192-bit) curve
 

// <i> Enable this setting if you need secp192r1 (NIST 192-bit) support using micro-ecc

#ifndef NRF_CRYPTO_BACKEND_MICRO_ECC_ECC_SECP192R1_ENABLED
#define NRF_CRYPTO_BACKEND_MICRO_ECC_ECC_SECP192R1_ENABLED 1
#endif

// <q> NRF_CRYPTO_BACKEND_MICRO_ECC_ECC_SECP224R1_ENABLED  - Enable secp224r1 (NIST 224-bit) curve
 

// <i> Enable this setting if you need secp224r1 (NIST 224-bit) support using micro-ecc

#ifndef NRF_CRYPTO_BACKEND_MICRO_ECC_ECC_SECP224R1_ENABLED
#define NRF_CRYPTO_BACKEND_MICRO_ECC_ECC_SECP224R1_ENABLED 1
#endif

// <q> NRF_CRYPTO_BACKEND_MICRO_ECC_ECC_SECP256R1_ENABLED  - Enable secp256r1 (NIST 256-bit) curve
 

// <i> Enable this setting if you need secp256r1 (NIST 256-bit) support using micro-ecc

#ifndef NRF_CRYPTO_BACKEND_MICRO_ECC_ECC_SECP256R1_ENABLED
#define NRF_CRYPTO_BACKEND_MICRO_ECC_ECC_SECP256R1_ENABLED 1
#endif

// <q> NRF_CRYPTO_BACKEND_MICRO_ECC_ECC_SECP256K1_ENABLED  - Enable secp256k1 (Koblitz 256-bit) curve
 

// <i> Enable this setting if you need secp256k1 (Koblitz 256-bit) support using micro-ecc

#ifndef NRF_CRYPTO_BACKEND_MICRO_ECC_ECC_SECP256K1_ENABLED
#define NRF_CRYPTO_BACKEND_MICRO_ECC_ECC_SECP256K1_ENABLED 1
#endif

// </e>

// <e> NRF_CRYPTO_BACKEND_NRF_HW_RNG_ENABLED - Enable the nRF HW RNG backend.

// <i> The nRF HW backend provide access to RNG peripheral in nRF5x devices.
//==========================================================
#ifndef NRF_CRYPTO_BACKEND_NRF_HW_RNG_ENABLED
#define NRF_CRYPTO_BACKEND_NRF_HW_RNG_ENABLED 0
#endif
// <q> NRF_CRYPTO_BACKEND_NRF_HW_RNG_MBEDTLS_CTR_DRBG_ENABLED  - Enable mbed TLS CTR-DRBG algorithm.
 

// <i> Enable mbed TLS CTR-DRBG standardized by NIST (NIST SP 800-90A Rev. 1). The nRF HW RNG is used as an entropy source for seeding.

#ifndef NRF_CRYPTO_BACKEND_NRF_HW_RNG_MBEDTLS_CTR_DRBG_ENABLED
#define NRF_CRYPTO_BACKEND_NRF_HW_RNG_MBEDTLS_CTR_DRBG_ENABLED 1
#endif

// </e>

// <e> NRF_CRYPTO_BACKEND_NRF_SW_ENABLED - Enable the legacy nRFx sw for crypto.

// <i> The nRF SW cryptography backend (only used in bootloader context).
//==========================================================
#ifndef NRF_CRYPTO_BACKEND_NRF_SW_ENABLED
#define NRF_CRYPTO_BACKEND_NRF_SW_ENABLED 0
#endif
// <q> NRF_CRYPTO_BACKEND_NRF_SW_HASH_SHA256_ENABLED  - nRF SW hash backend support for SHA-256
 

// <i> The nRF SW backend provide access to nRF SDK legacy hash implementation of SHA-256.

#ifndef NRF_CRYPTO_BACKEND_NRF_SW_HASH_SHA256_ENABLED
#define NRF_CRYPTO_BACKEND_NRF_SW_HASH_SHA256_ENABLED 1
#endif

// </e>

// <e> NRF_CRYPTO_BACKEND_OBERON_ENABLED - Enable the Oberon backend

// <i> The Oberon backend
//==========================================================
#ifndef NRF_CRYPTO_BACKEND_OBERON_ENABLED
#define NRF_CRYPTO_BACKEND_OBERON_ENABLED 0
#endif
// <q> NRF_CRYPTO_BACKEND_OBERON_CHACHA_POLY_ENABLED  - Enable the CHACHA-POLY mode using Oberon.
 

#ifndef NRF_CRYPTO_BACKEND_OBERON_CHACHA_POLY_ENABLED
#define NRF_CRYPTO_BACKEND_OBERON_CHACHA_POLY_ENABLED 1
#endif

// <q> NRF_CRYPTO_BACKEND_OBERON_ECC_SECP256R1_ENABLED  - Enable secp256r1 curve
 

// <i> Enable this setting if you need secp256r1 curve support using Oberon library

#ifndef NRF_CRYPTO_BACKEND_OBERON_ECC_SECP256R1_ENABLED
#define NRF_CRYPTO_BACKEND_OBERON_ECC_SECP256R1_ENABLED 1
#endif

// <q> NRF_CRYPTO_BACKEND_OBERON_ECC_CURVE25519_ENABLED  - Enable Curve25519 ECDH
 

// <i> Enable this setting if you need Curve25519 ECDH support using Oberon library

#ifndef NRF_CRYPTO_BACKEND_OBERON_ECC_CURVE25519_ENABLED
#define NRF_CRYPTO_BACKEND_OBERON_ECC_CURVE25519_ENABLED 1
#endif

// <q> NRF_CRYPTO_BACKEND_OBERON_ECC_ED25519_ENABLED  - Enable Ed25519 signature scheme
 

// <i> Enable this setting if you need Ed25519 support using Oberon library

#ifndef NRF_CRYPTO_BACKEND_OBERON_ECC_ED25519_ENABLED
#define NRF_CRYPTO_BACKEND_OBERON_ECC_ED25519_ENABLED 1
#endif

// <q> NRF_CRYPTO_BACKEND_OBERON_HASH_SHA256_ENABLED  - Oberon SHA-256 hash functionality
 

// <i> Oberon backend implementation for SHA-256.

#ifndef NRF_CRYPTO_BACKEND_OBERON_HASH_SHA256_ENABLED
#define NRF_CRYPTO_BACKEND_OBERON_HASH_SHA256_ENABLED 1
#endif

// <q> NRF_CRYPTO_BACKEND_OBERON_HASH_SHA512_ENABLED  - Oberon SHA-512 hash functionality
 

// <i> Oberon backend implementation for SHA-512.

#ifndef NRF_CRYPTO_BACKEND_OBERON_HASH_SHA512_ENABLED
#define NRF_CRYPTO_BACKEND_OBERON_HASH_SHA512_ENABLED 1
#endif

// <q> NRF_CRYPTO_BACKEND_OBERON_HMAC_SHA256_ENABLED  - Oberon HMAC using SHA-256
 

// <i> Oberon backend implementation for HMAC using SHA-256.

#ifndef NRF_CRYPTO_BACKEND_OBERON_HMAC_SHA256_ENABLED
#define NRF_CRYPTO_BACKEND_OBERON_HMAC_SHA256_ENABLED 1
#endif

// <q> NRF_CRYPTO_BACKEND_OBERON_HMAC_SHA512_ENABLED  - Oberon HMAC using SHA-512
 

// <i> Oberon backend implementation for HMAC using SHA-512.

#ifndef NRF_CRYPTO_BACKEND_OBERON_HMAC_SHA512_ENABLED
#define NRF_CRYPTO_BACKEND_OBERON_HMAC_SHA512_ENABLED 1
#endif

// </e>

// <e> NRF_CRYPTO_BACKEND_OPTIGA_ENABLED - Enable the nrf_crypto Optiga Trust X backend.

// <i> Enables the nrf_crypto backend for Optiga Trust X devices.
//==========================================================
#ifndef NRF_CRYPTO_BACKEND_OPTIGA_ENABLED
#define NRF_CRYPTO_BACKEND_OPTIGA_ENABLED 0
#endif
// <q> NRF_CRYPTO_BACKEND_OPTIGA_RNG_ENABLED  - Optiga backend support for RNG
 

// <i> The Optiga backend provide external chip RNG.

#ifndef NRF_CRYPTO_BACKEND_OPTIGA_RNG_ENABLED
#define NRF_CRYPTO_BACKEND_OPTIGA_RNG_ENABLED 0
#endif

// <q> NRF_CRYPTO_BACKEND_OPTIGA_ECC_SECP256R1_ENABLED  - Optiga backend support for ECC secp256r1
 

// <i> The Optiga backend provide external chip ECC using secp256r1.

#ifndef NRF_CRYPTO_BACKEND_OPTIGA_ECC_SECP256R1_ENABLED
#define NRF_CRYPTO_BACKEND_OPTIGA_ECC_SECP256R1_ENABLED 1
#endif

// </e>

// <q> NRF_CRYPTO_CURVE25519_BIG_ENDIAN_ENABLED  - Big-endian byte order in raw Curve25519 data
 

// <i> Enable big-endian byte order in Curve25519 API, if set to 1. Use little-endian, if set to 0.

#ifndef NRF_CRYPTO_CURVE25519_BIG_ENDIAN_ENABLED
#define NRF_CRYPTO_CURVE25519_BIG_ENDIAN_ENABLED 0
#endif

// </e>

// </h> 
//==========================================================

// <h> nRF_DFU 

//==========================================================
// <h> ble_dfu - Device Firmware Update

//==========================================================
// <q> BLE_DFU_ENABLED  - Enable DFU Service.
 

#ifndef BLE_DFU_ENABLED
#define BLE_DFU_ENABLED 0
#endif

// <q> NRF_DFU_BLE_BUTTONLESS_SUPPORTS_BONDS  - Buttonless DFU supports bonds.
 

#ifndef NRF_DFU_BLE_BUTTONLESS_SUPPORTS_BONDS
#define NRF_DFU_BLE_BUTTONLESS_SUPPORTS_BONDS 0
#endif

// </h> 
//==========================================================

// </h> 
//==========================================================

// <h> nRF_Drivers 

//==========================================================
// <e> COMP_ENABLED - nrf_drv_comp - COMP peripheral driver - legacy layer
//==========================================================
#ifndef COMP_ENABLED
#define COMP_ENABLED 0
#endif
// <o> COMP_CONFIG_REF  - Reference voltage
 
// <0=> Internal 1.2V 
// <1=> Internal 1.8V 
// <2=> Internal 2.4V 
// <4=> VDD 
// <7=> ARef 

#ifndef COMP_CONFIG_REF
#define COMP_CONFIG_REF 1
#endif

// <o> COMP_CONFIG_MAIN_MODE  - Main mode
 
// <0=> Single ended 
// <1=> Differential 

#ifndef COMP_CONFIG_MAIN_MODE
#define COMP_CONFIG_MAIN_MODE 0
#endif

// <o> COMP_CONFIG_SPEED_MODE  - Speed mode
 
// <0=> Low power 
// <1=> Normal 
// <2=> High speed 

#ifndef COMP_CONFIG_SPEED_MODE
#define COMP_CONFIG_SPEED_MODE 2
#endif

// <o> COMP_CONFIG_HYST  - Hystheresis
 
// <0=> No 
// <1=> 50mV 

#ifndef COMP_CONFIG_HYST
#define COMP_CONFIG_HYST 0
#endif

// <o> COMP_CONFIG_ISOURCE  - Current Source
 
// <0=> Off 
// <1=> 2.5 uA 
// <2=> 5 uA 
// <3=> 10 uA 

#ifndef COMP_CONFIG_ISOURCE
#define COMP_CONFIG_ISOURCE 0
#endif

// <o> COMP_CONFIG_INPUT  - Analog input
 
// <0=> 0 
// <1=> 1 
// <2=> 2 
// <3=> 3 
// <4=> 4 
// <5=> 5 
// <6=> 6 
// <7=> 7 

#ifndef COMP_CONFIG_INPUT
#define COMP_CONFIG_INPUT 0
#endif

// <o> COMP_CONFIG_IRQ_PRIORITY  - Interrupt priority
 

// <i> Priorities 0,2 (nRF51) and 0,1,4,5 (nRF52) are reserved for SoftDevice
// <0=> 0 (highest) 
// <1=> 1 
// <2=> 2 
// <3=> 3 
// <4=> 4 
// <5=> 5 
// <6=> 6 
// <7=> 7 

#ifndef COMP_CONFIG_IRQ_PRIORITY
#define COMP_CONFIG_IRQ_PRIORITY 6
#endif

// </e>

// <q> EGU_ENABLED  - nrf_drv_swi - SWI(EGU) peripheral driver - legacy layer
 

#ifndef EGU_ENABLED
#define EGU_ENABLED 0
#endif

// <e> GPIOTE_ENABLED - nrf_drv_gpiote - GPIOTE peripheral driver - legacy layer
//==========================================================
#ifndef GPIOTE_ENABLED
#define GPIOTE_ENABLED 1
#endif
// <o> GPIOTE_CONFIG_NUM_OF_LOW_POWER_EVENTS - Number of lower power input pins 
#ifndef GPIOTE_CONFIG_NUM_OF_LOW_POWER_EVENTS
#define GPIOTE_CONFIG_NUM_OF_LOW_POWER_EVENTS 1
#endif

// <o> GPIOTE_CONFIG_IRQ_PRIORITY  - Interrupt priority
 

// <i> Priorities 0,2 (nRF51) and 0,1,4,5 (nRF52) are reserved for SoftDevice
// <0=> 0 (highest) 
// <1=> 1 
// <2=> 2 
// <3=> 3 
// <4=> 4 
// <5=> 5 
// <6=> 6 
// <7=> 7 

#ifndef GPIOTE_CONFIG_IRQ_PRIORITY
#define GPIOTE_CONFIG_IRQ_PRIORITY 6
#endif

// </e>

// <e> I2S_ENABLED - nrf_drv_i2s - I2S peripheral driver - legacy layer
//==========================================================
#ifndef I2S_ENABLED
#define I2S_ENABLED 0
#endif
// <o> I2S_CONFIG_SCK_PIN - SCK pin  <0-31> 


#ifndef I2S_CONFIG_SCK_PIN
#define I2S_CONFIG_SCK_PIN 31
#endif

// <o> I2S_CONFIG_LRCK_PIN - LRCK pin  <1-31> 


#ifndef I2S_CONFIG_LRCK_PIN
#define I2S_CONFIG_LRCK_PIN 30
#endif

// <o> I2S_CONFIG_MCK_PIN - MCK pin 
#ifndef I2S_CONFIG_MCK_PIN
#define I2S_CONFIG_MCK_PIN 255
#endif

// <o> I2S_CONFIG_SDOUT_PIN - SDOUT pin  <0-31> 


#ifndef I2S_CONFIG_SDOUT_PIN
#define I2S_CONFIG_SDOUT_PIN 29
#endif

// <o> I2S_CONFIG_SDIN_PIN - SDIN pin  <0-31> 


#ifndef I2S_CONFIG_SDIN_PIN
#define I2S_CONFIG_SDIN_PIN 28
#endif

// <o> I2S_CONFIG_MASTER  - Mode
 
// <0=> Master 
// <1=> Slave 

#ifndef I2S_CONFIG_MASTER
#define I2S_CONFIG_MASTER 0
#endif

// <o> I2S_CONFIG_FORMAT  - Format
 
// <0=> I2S 
// <1=> Aligned 

#ifndef I2S_CONFIG_FORMAT
#define I2S_CONFIG_FORMAT 0
#endif

// <o> I2S_CONFIG_ALIGN  - Alignment
 
// <0=> Left 
// <1=> Right 

#ifndef I2S_CONFIG_ALIGN
#define I2S_CONFIG_ALIGN 0
#endif

// <o> I2S_CONFIG_SWIDTH  - Sample width (bits)
 
// <0=> 8 
// <1=> 16 
// <2=> 24 

#ifndef I2S_CONFIG_SWIDTH
#define I2S_CONFIG_SWIDTH 1
#endif

// <o> I2S_CONFIG_CHANNELS  - Channels
 
// <0=> Stereo 
// <1=> Left 
// <2=> Right 

#ifndef I2S_CONFIG_CHANNELS
#define I2S_CONFIG_CHANNELS 1
#endif

// <o> I2S_CONFIG_MCK_SETUP  - MCK behavior
 
// <0=> Disabled 
// <2147483648=> 32MHz/2 
// <1342177280=> 32MHz/3 
// <1073741824=> 32MHz/4 
// <805306368=> 32MHz/5 
// <671088640=> 32MHz/6 
// <536870912=> 32MHz/8 
// <402653184=> 32MHz/10 
// <369098752=> 32MHz/11 
// <285212672=> 32MHz/15 
// <268435456=> 32MHz/16 
// <201326592=> 32MHz/21 
// <184549376=> 32MHz/23 
// <142606336=> 32MHz/30 
// <138412032=> 32MHz/31 
// <134217728=> 32MHz/32 
// <100663296=> 32MHz/42 
// <68157440=> 32MHz/63 
// <34340864=> 32MHz/125 

#ifndef I2S_CONFIG_MCK_SETUP
#define I2S_CONFIG_MCK_SETUP 536870912
#endif

// <o> I2S_CONFIG_RATIO  - MCK/LRCK ratio
 
// <0=> 32x 
// <1=> 48x 
// <2=> 64x 
// <3=> 96x 
// <4=> 128x 
// <5=> 192x 
// <6=> 256x 
// <7=> 384x 
// <8=> 512x 

#ifndef I2S_CONFIG_RATIO
#define I2S_CONFIG_RATIO 2000
#endif

// <o> I2S_CONFIG_IRQ_PRIORITY  - Interrupt priority
 

// <i> Priorities 0,2 (nRF51) and 0,1,4,5 (nRF52) are reserved for SoftDevice
// <0=> 0 (highest) 
// <1=> 1 
// <2=> 2 
// <3=> 3 
// <4=> 4 
// <5=> 5 
// <6=> 6 
// <7=> 7 

#ifndef I2S_CONFIG_IRQ_PRIORITY
#define I2S_CONFIG_IRQ_PRIORITY 6
#endif

// <e> I2S_CONFIG_LOG_ENABLED - Enables logging in the module.
//==========================================================
#ifndef I2S_CONFIG_LOG_ENABLED
#define I2S_CONFIG_LOG_ENABLED 0
#endif
// <o> I2S_CONFIG_LOG_LEVEL  - Default Severity level
 
// <0=> Off 
// <1=> Error 
// <2=> Warning 
// <3=> Info 
// <4=> Debug 

#ifndef I2S_CONFIG_LOG_LEVEL
#define I2S_CONFIG_LOG_LEVEL 3
#endif

// <o> I2S_CONFIG_INFO_COLOR  - ANSI escape code prefix.
 
// <0=> Default 
// <1=> Black 
// <2=> Red 
// <3=> Green 
// <4=> Yellow 
// <5=> Blue 
// <6=> Magenta 
// <7=> Cyan 
// <8=> White 

#ifndef I2S_CONFIG_INFO_COLOR
#define I2S_CONFIG_INFO_COLOR 0
#endif

// <o> I2S_CONFIG_DEBUG_COLOR  - ANSI escape code prefix.
 
// <0=> Default 
// <1=> Black 
// <2=> Red 
// <3=> Green 
// <4=> Yellow 
// <5=> Blue 
// <6=> Magenta 
// <7=> Cyan 
// <8=> White 

#ifndef I2S_CONFIG_DEBUG_COLOR
#define I2S_CONFIG_DEBUG_COLOR 0
#endif

// </e>

// </e>

// <e> LPCOMP_ENABLED - nrf_drv_lpcomp - LPCOMP peripheral driver - legacy layer
//==========================================================
#ifndef LPCOMP_ENABLED
#define LPCOMP_ENABLED 0
#endif
// <o> LPCOMP_CONFIG_REFERENCE  - Reference voltage
 
// <0=> Supply 1/8 
// <1=> Supply 2/8 
// <2=> Supply 3/8 
// <3=> Supply 4/8 
// <4=> Supply 5/8 
// <5=> Supply 6/8 
// <6=> Supply 7/8 
// <8=> Supply 1/16 (nRF52) 
// <9=> Supply 3/16 (nRF52) 
// <10=> Supply 5/16 (nRF52) 
// <11=> Supply 7/16 (nRF52) 
// <12=> Supply 9/16 (nRF52) 
// <13=> Supply 11/16 (nRF52) 
// <14=> Supply 13/16 (nRF52) 
// <15=> Supply 15/16 (nRF52) 
// <7=> External Ref 0 
// <65543=> External Ref 1 

#ifndef LPCOMP_CONFIG_REFERENCE
#define LPCOMP_CONFIG_REFERENCE 3
#endif

// <o> LPCOMP_CONFIG_DETECTION  - Detection
 
// <0=> Crossing 
// <1=> Up 
// <2=> Down 

#ifndef LPCOMP_CONFIG_DETECTION
#define LPCOMP_CONFIG_DETECTION 2
#endif

// <o> LPCOMP_CONFIG_INPUT  - Analog input
 
// <0=> 0 
// <1=> 1 
// <2=> 2 
// <3=> 3 
// <4=> 4 
// <5=> 5 
// <6=> 6 
// <7=> 7 

#ifndef LPCOMP_CONFIG_INPUT
#define LPCOMP_CONFIG_INPUT 0
#endif

// <q> LPCOMP_CONFIG_HYST  - Hysteresis
 

#ifndef LPCOMP_CONFIG_HYST
#define LPCOMP_CONFIG_HYST 0
#endif

// <o> LPCOMP_CONFIG_IRQ_PRIORITY  - Interrupt priority
 

// <i> Priorities 0,2 (nRF51) and 0,1,4,5 (nRF52) are reserved for SoftDevice
// <0=> 0 (highest) 
// <1=> 1 
// <2=> 2 
// <3=> 3 
// <4=> 4 
// <5=> 5 
// <6=> 6 
// <7=> 7 

#ifndef LPCOMP_CONFIG_IRQ_PRIORITY
#define LPCOMP_CONFIG_IRQ_PRIORITY 6
#endif

// </e>

// <e> NRFX_CLOCK_ENABLED - nrfx_clock - CLOCK peripheral driver
//==========================================================
#ifndef NRFX_CLOCK_ENABLED
#define NRFX_CLOCK_ENABLED 1
#endif
// <o> NRFX_CLOCK_CONFIG_LF_SRC  - LF Clock Source
 
// <0=> RC 
// <1=> XTAL 
// <2=> Synth 
// <131073=> External Low Swing 
// <196609=> External Full Swing 

#ifndef NRFX_CLOCK_CONFIG_LF_SRC
#define NRFX_CLOCK_CONFIG_LF_SRC 1
#endif

// <o> NRFX_CLOCK_CONFIG_IRQ_PRIORITY  - Interrupt priority
 
// <0=> 0 (highest) 
// <1=> 1 
// <2=> 2 
// <3=> 3 
// <4=> 4 
// <5=> 5 
// <6=> 6 
// <7=> 7 

#ifndef NRFX_CLOCK_CONFIG_IRQ_PRIORITY
#define NRFX_CLOCK_CONFIG_IRQ_PRIORITY 6
#endif

// <e> NRFX_CLOCK_CONFIG_LOG_ENABLED - Enables logging in the module.
//==========================================================
#ifndef NRFX_CLOCK_CONFIG_LOG_ENABLED
#define NRFX_CLOCK_CONFIG_LOG_ENABLED 0
#endif
// <o> NRFX_CLOCK_CONFIG_LOG_LEVEL  - Default Severity level
 
// <0=> Off 
// <1=> Error 
// <2=> Warning 
// <3=> Info 
// <4=> Debug 

#ifndef NRFX_CLOCK_CONFIG_LOG_LEVEL
#define NRFX_CLOCK_CONFIG_LOG_LEVEL 3
#endif

// <o> NRFX_CLOCK_CONFIG_INFO_COLOR  - ANSI escape code prefix.
 
// <0=> Default 
// <1=> Black 
// <2=> Red 
// <3=> Green 
// <4=> Yellow 
// <5=> Blue 
// <6=> Magenta 
// <7=> Cyan 
// <8=> White 

#ifndef NRFX_CLOCK_CONFIG_INFO_COLOR
#define NRFX_CLOCK_CONFIG_INFO_COLOR 0
#endif

// <o> NRFX_CLOCK_CONFIG_DEBUG_COLOR  - ANSI escape code prefix.
 
// <0=> Default 
// <1=> Black 
// <2=> Red 
// <3=> Green 
// <4=> Yellow 
// <5=> Blue 
// <6=> Magenta 
// <7=> Cyan 
// <8=> White 

#ifndef NRFX_CLOCK_CONFIG_DEBUG_COLOR
#define NRFX_CLOCK_CONFIG_DEBUG_COLOR 0
#endif

// </e>

// </e>

// <e> NRFX_COMP_ENABLED - nrfx_comp - COMP peripheral driver
//==========================================================
#ifndef NRFX_COMP_ENABLED
#define NRFX_COMP_ENABLED 0
#endif
// <o> NRFX_COMP_CONFIG_REF  - Reference voltage
 
// <0=> Internal 1.2V 
// <1=> Internal 1.8V 
// <2=> Internal 2.4V 
// <4=> VDD 
// <7=> ARef 

#ifndef NRFX_COMP_CONFIG_REF
#define NRFX_COMP_CONFIG_REF 1
#endif

// <o> NRFX_COMP_CONFIG_MAIN_MODE  - Main mode
 
// <0=> Single ended 
// <1=> Differential 

#ifndef NRFX_COMP_CONFIG_MAIN_MODE
#define NRFX_COMP_CONFIG_MAIN_MODE 0
#endif

// <o> NRFX_COMP_CONFIG_SPEED_MODE  - Speed mode
 
// <0=> Low power 
// <1=> Normal 
// <2=> High speed 

#ifndef NRFX_COMP_CONFIG_SPEED_MODE
#define NRFX_COMP_CONFIG_SPEED_MODE 2
#endif

// <o> NRFX_COMP_CONFIG_HYST  - Hystheresis
 
// <0=> No 
// <1=> 50mV 

#ifndef NRFX_COMP_CONFIG_HYST
#define NRFX_COMP_CONFIG_HYST 0
#endif

// <o> NRFX_COMP_CONFIG_ISOURCE  - Current Source
 
// <0=> Off 
// <1=> 2.5 uA 
// <2=> 5 uA 
// <3=> 10 uA 

#ifndef NRFX_COMP_CONFIG_ISOURCE
#define NRFX_COMP_CONFIG_ISOURCE 0
#endif

// <o> NRFX_COMP_CONFIG_INPUT  - Analog input
 
// <0=> 0 
// <1=> 1 
// <2=> 2 
// <3=> 3 
// <4=> 4 
// <5=> 5 
// <6=> 6 
// <7=> 7 

#ifndef NRFX_COMP_CONFIG_INPUT
#define NRFX_COMP_CONFIG_INPUT 0
#endif

// <o> NRFX_COMP_CONFIG_IRQ_PRIORITY  - Interrupt priority
 
// <0=> 0 (highest) 
// <1=> 1 
// <2=> 2 
// <3=> 3 
// <4=> 4 
// <5=> 5 
// <6=> 6 
// <7=> 7 

#ifndef NRFX_COMP_CONFIG_IRQ_PRIORITY
#define NRFX_COMP_CONFIG_IRQ_PRIORITY 6
#endif

// <e> NRFX_COMP_CONFIG_LOG_ENABLED - Enables logging in the module.
//==========================================================
#ifndef NRFX_COMP_CONFIG_LOG_ENABLED
#define NRFX_COMP_CONFIG_LOG_ENABLED 0
#endif
// <o> NRFX_COMP_CONFIG_LOG_LEVEL  - Default Severity level
 
// <0=> Off 
// <1=> Error 
// <2=> Warning 
// <3=> Info 
// <4=> Debug 

#ifndef NRFX_COMP_CONFIG_LOG_LEVEL
#define NRFX_COMP_CONFIG_LOG_LEVEL 3
#endif

// <o> NRFX_COMP_CONFIG_INFO_COLOR  - ANSI escape code prefix.
 
// <0=> Default 
// <1=> Black 
// <2=> Red 
// <3=> Green 
// <4=> Yellow 
// <5=> Blue 
// <6=> Magenta 
// <7=> Cyan 
// <8=> White 

#ifndef NRFX_COMP_CONFIG_INFO_COLOR
#define NRFX_COMP_CONFIG_INFO_COLOR 0
#endif

// <o> NRFX_COMP_CONFIG_DEBUG_COLOR  - ANSI escape code prefix.
 
// <0=> Default 
// <1=> Black 
// <2=> Red 
// <3=> Green 
// <4=> Yellow 
// <5=> Blue 
// <6=> Magenta 
// <7=> Cyan 
// <8=> White 

#ifndef NRFX_COMP_CONFIG_DEBUG_COLOR
#define NRFX_COMP_CONFIG_DEBUG_COLOR 0
#endif

// </e>

// </e>

// <e> NRFX_GPIOTE_ENABLED - nrfx_gpiote - GPIOTE peripheral driver
//==========================================================
#ifndef NRFX_GPIOTE_ENABLED
#define NRFX_GPIOTE_ENABLED 1
#endif
// <o> NRFX_GPIOTE_CONFIG_NUM_OF_LOW_POWER_EVENTS - Number of lower power input pins 
#ifndef NRFX_GPIOTE_CONFIG_NUM_OF_LOW_POWER_EVENTS
#define NRFX_GPIOTE_CONFIG_NUM_OF_LOW_POWER_EVENTS 1
#endif

// <o> NRFX_GPIOTE_CONFIG_IRQ_PRIORITY  - Interrupt priority
 
// <0=> 0 (highest) 
// <1=> 1 
// <2=> 2 
// <3=> 3 
// <4=> 4 
// <5=> 5 
// <6=> 6 
// <7=> 7 

#ifndef NRFX_GPIOTE_CONFIG_IRQ_PRIORITY
#define NRFX_GPIOTE_CONFIG_IRQ_PRIORITY 6
#endif

// <e> NRFX_GPIOTE_CONFIG_LOG_ENABLED - Enables logging in the module.
//==========================================================
#ifndef NRFX_GPIOTE_CONFIG_LOG_ENABLED
#define NRFX_GPIOTE_CONFIG_LOG_ENABLED 0
#endif
// <o> NRFX_GPIOTE_CONFIG_LOG_LEVEL  - Default Severity level
 
// <0=> Off 
// <1=> Error 
// <2=> Warning 
// <3=> Info 
// <4=> Debug 

#ifndef NRFX_GPIOTE_CONFIG_LOG_LEVEL
#define NRFX_GPIOTE_CONFIG_LOG_LEVEL 3
#endif

// <o> NRFX_GPIOTE_CONFIG_INFO_COLOR  - ANSI escape code prefix.
 
// <0=> Default 
// <1=> Black 
// <2=> Red 
// <3=> Green 
// <4=> Yellow 
// <5=> Blue 
// <6=> Magenta 
// <7=> Cyan 
// <8=> White 

#ifndef NRFX_GPIOTE_CONFIG_INFO_COLOR
#define NRFX_GPIOTE_CONFIG_INFO_COLOR 0
#endif

// <o> NRFX_GPIOTE_CONFIG_DEBUG_COLOR  - ANSI escape code prefix.
 
// <0=> Default 
// <1=> Black 
// <2=> Red 
// <3=> Green 
// <4=> Yellow 
// <5=> Blue 
// <6=> Magenta 
// <7=> Cyan 
// <8=> White 

#ifndef NRFX_GPIOTE_CONFIG_DEBUG_COLOR
#define NRFX_GPIOTE_CONFIG_DEBUG_COLOR 0
#endif

// </e>

// </e>

// <e> NRFX_I2S_ENABLED - nrfx_i2s - I2S peripheral driver
//==========================================================
#ifndef NRFX_I2S_ENABLED
#define NRFX_I2S_ENABLED 0
#endif
// <o> NRFX_I2S_CONFIG_SCK_PIN - SCK pin  <0-31> 


#ifndef NRFX_I2S_CONFIG_SCK_PIN
#define NRFX_I2S_CONFIG_SCK_PIN 31
#endif

// <o> NRFX_I2S_CONFIG_LRCK_PIN - LRCK pin  <1-31> 


#ifndef NRFX_I2S_CONFIG_LRCK_PIN
#define NRFX_I2S_CONFIG_LRCK_PIN 30
#endif

// <o> NRFX_I2S_CONFIG_MCK_PIN - MCK pin 
#ifndef NRFX_I2S_CONFIG_MCK_PIN
#define NRFX_I2S_CONFIG_MCK_PIN 255
#endif

// <o> NRFX_I2S_CONFIG_SDOUT_PIN - SDOUT pin  <0-31> 


#ifndef NRFX_I2S_CONFIG_SDOUT_PIN
#define NRFX_I2S_CONFIG_SDOUT_PIN 29
#endif

// <o> NRFX_I2S_CONFIG_SDIN_PIN - SDIN pin  <0-31> 


#ifndef NRFX_I2S_CONFIG_SDIN_PIN
#define NRFX_I2S_CONFIG_SDIN_PIN 28
#endif

// <o> NRFX_I2S_CONFIG_MASTER  - Mode
 
// <0=> Master 
// <1=> Slave 

#ifndef NRFX_I2S_CONFIG_MASTER
#define NRFX_I2S_CONFIG_MASTER 0
#endif

// <o> NRFX_I2S_CONFIG_FORMAT  - Format
 
// <0=> I2S 
// <1=> Aligned 

#ifndef NRFX_I2S_CONFIG_FORMAT
#define NRFX_I2S_CONFIG_FORMAT 0
#endif

// <o> NRFX_I2S_CONFIG_ALIGN  - Alignment
 
// <0=> Left 
// <1=> Right 

#ifndef NRFX_I2S_CONFIG_ALIGN
#define NRFX_I2S_CONFIG_ALIGN 0
#endif

// <o> NRFX_I2S_CONFIG_SWIDTH  - Sample width (bits)
 
// <0=> 8 
// <1=> 16 
// <2=> 24 

#ifndef NRFX_I2S_CONFIG_SWIDTH
#define NRFX_I2S_CONFIG_SWIDTH 1
#endif

// <o> NRFX_I2S_CONFIG_CHANNELS  - Channels
 
// <0=> Stereo 
// <1=> Left 
// <2=> Right 

#ifndef NRFX_I2S_CONFIG_CHANNELS
#define NRFX_I2S_CONFIG_CHANNELS 1
#endif

// <o> NRFX_I2S_CONFIG_MCK_SETUP  - MCK behavior
 
// <0=> Disabled 
// <2147483648=> 32MHz/2 
// <1342177280=> 32MHz/3 
// <1073741824=> 32MHz/4 
// <805306368=> 32MHz/5 
// <671088640=> 32MHz/6 
// <536870912=> 32MHz/8 
// <402653184=> 32MHz/10 
// <369098752=> 32MHz/11 
// <285212672=> 32MHz/15 
// <268435456=> 32MHz/16 
// <201326592=> 32MHz/21 
// <184549376=> 32MHz/23 
// <142606336=> 32MHz/30 
// <138412032=> 32MHz/31 
// <134217728=> 32MHz/32 
// <100663296=> 32MHz/42 
// <68157440=> 32MHz/63 
// <34340864=> 32MHz/125 

#ifndef NRFX_I2S_CONFIG_MCK_SETUP
#define NRFX_I2S_CONFIG_MCK_SETUP 536870912
#endif

// <o> NRFX_I2S_CONFIG_RATIO  - MCK/LRCK ratio
 
// <0=> 32x 
// <1=> 48x 
// <2=> 64x 
// <3=> 96x 
// <4=> 128x 
// <5=> 192x 
// <6=> 256x 
// <7=> 384x 
// <8=> 512x 

#ifndef NRFX_I2S_CONFIG_RATIO
#define NRFX_I2S_CONFIG_RATIO 2000
#endif

// <o> NRFX_I2S_CONFIG_IRQ_PRIORITY  - Interrupt priority
 
// <0=> 0 (highest) 
// <1=> 1 
// <2=> 2 
// <3=> 3 
// <4=> 4 
// <5=> 5 
// <6=> 6 
// <7=> 7 

#ifndef NRFX_I2S_CONFIG_IRQ_PRIORITY
#define NRFX_I2S_CONFIG_IRQ_PRIORITY 6
#endif

// <e> NRFX_I2S_CONFIG_LOG_ENABLED - Enables logging in the module.
//==========================================================
#ifndef NRFX_I2S_CONFIG_LOG_ENABLED
#define NRFX_I2S_CONFIG_LOG_ENABLED 0
#endif
// <o> NRFX_I2S_CONFIG_LOG_LEVEL  - Default Severity level
 
// <0=> Off 
// <1=> Error 
// <2=> Warning 
// <3=> Info 
// <4=> Debug 

#ifndef NRFX_I2S_CONFIG_LOG_LEVEL
#define NRFX_I2S_CONFIG_LOG_LEVEL 3
#endif

// <o> NRFX_I2S_CONFIG_INFO_COLOR  - ANSI escape code prefix.
 
// <0=> Default 
// <1=> Black 
// <2=> Red 
// <3=> Green 
// <4=> Yellow 
// <5=> Blue 
// <6=> Magenta 
// <7=> Cyan 
// <8=> White 

#ifndef NRFX_I2S_CONFIG_INFO_COLOR
#define NRFX_I2S_CONFIG_INFO_COLOR 0
#endif

// <o> NRFX_I2S_CONFIG_DEBUG_COLOR  - ANSI escape code prefix.
 
// <0=> Default 
// <1=> Black 
// <2=> Red 
// <3=> Green 
// <4=> Yellow 
// <5=> Blue 
// <6=> Magenta 
// <7=> Cyan 
// <8=> White 

#ifndef NRFX_I2S_CONFIG_DEBUG_COLOR
#define NRFX_I2S_CONFIG_DEBUG_COLOR 0
#endif

// </e>

// </e>

// <e> NRFX_LPCOMP_ENABLED - nrfx_lpcomp - LPCOMP peripheral driver
//==========================================================
#ifndef NRFX_LPCOMP_ENABLED
#define NRFX_LPCOMP_ENABLED 0
#endif
// <o> NRFX_LPCOMP_CONFIG_REFERENCE  - Reference voltage
 
// <0=> Supply 1/8 
// <1=> Supply 2/8 
// <2=> Supply 3/8 
// <3=> Supply 4/8 
// <4=> Supply 5/8 
// <5=> Supply 6/8 
// <6=> Supply 7/8 
// <8=> Supply 1/16 (nRF52) 
// <9=> Supply 3/16 (nRF52) 
// <10=> Supply 5/16 (nRF52) 
// <11=> Supply 7/16 (nRF52) 
// <12=> Supply 9/16 (nRF52) 
// <13=> Supply 11/16 (nRF52) 
// <14=> Supply 13/16 (nRF52) 
// <15=> Supply 15/16 (nRF52) 
// <7=> External Ref 0 
// <65543=> External Ref 1 

#ifndef NRFX_LPCOMP_CONFIG_REFERENCE
#define NRFX_LPCOMP_CONFIG_REFERENCE 3
#endif

// <o> NRFX_LPCOMP_CONFIG_DETECTION  - Detection
 
// <0=> Crossing 
// <1=> Up 
// <2=> Down 

#ifndef NRFX_LPCOMP_CONFIG_DETECTION
#define NRFX_LPCOMP_CONFIG_DETECTION 2
#endif

// <o> NRFX_LPCOMP_CONFIG_INPUT  - Analog input
 
// <0=> 0 
// <1=> 1 
// <2=> 2 
// <3=> 3 
// <4=> 4 
// <5=> 5 
// <6=> 6 
// <7=> 7 

#ifndef NRFX_LPCOMP_CONFIG_INPUT
#define NRFX_LPCOMP_CONFIG_INPUT 0
#endif

// <q> NRFX_LPCOMP_CONFIG_HYST  - Hysteresis
 

#ifndef NRFX_LPCOMP_CONFIG_HYST
#define NRFX_LPCOMP_CONFIG_HYST 0
#endif

// <o> NRFX_LPCOMP_CONFIG_IRQ_PRIORITY  - Interrupt priority
 
// <0=> 0 (highest) 
// <1=> 1 
// <2=> 2 
// <3=> 3 
// <4=> 4 
// <5=> 5 
// <6=> 6 
// <7=> 7 

#ifndef NRFX_LPCOMP_CONFIG_IRQ_PRIORITY
#define NRFX_LPCOMP_CONFIG_IRQ_PRIORITY 6
#endif

// <e> NRFX_LPCOMP_CONFIG_LOG_ENABLED - Enables logging in the module.
//==========================================================
#ifndef NRFX_LPCOMP_CONFIG_LOG_ENABLED
#define NRFX_LPCOMP_CONFIG_LOG_ENABLED 0
#endif
// <o> NRFX_LPCOMP_CONFIG_LOG_LEVEL  - Default Severity level
 
// <0=> Off 
// <1=> Error 
// <2=> Warning 
// <3=> Info 
// <4=> Debug 

#ifndef NRFX_LPCOMP_CONFIG_LOG_LEVEL
#define NRFX_LPCOMP_CONFIG_LOG_LEVEL 3
#endif

// <o> NRFX_LPCOMP_CONFIG_INFO_COLOR  - ANSI escape code prefix.
 
// <0=> Default 
// <1=> Black 
// <2=> Red 
// <3=> Green 
// <4=> Yellow 
// <5=> Blue 
// <6=> Magenta 
// <7=> Cyan 
// <8=> White 

#ifndef NRFX_LPCOMP_CONFIG_INFO_COLOR
#define NRFX_LPCOMP_CONFIG_INFO_COLOR 0
#endif

// <o> NRFX_LPCOMP_CONFIG_DEBUG_COLOR  - ANSI escape code prefix.
 
// <0=> Default 
// <1=> Black 
// <2=> Red 
// <3=> Green 
// <4=> Yellow 
// <5=> Blue 
// <6=> Magenta 
// <7=> Cyan 
// <8=> White 

#ifndef NRFX_LPCOMP_CONFIG_DEBUG_COLOR
#define NRFX_LPCOMP_CONFIG_DEBUG_COLOR 0
#endif

// </e>

// </e>

// <e> NRFX_NFCT_ENABLED - nrfx_nfct - NFCT peripheral driver
//==========================================================
#ifndef NRFX_NFCT_ENABLED
#define NRFX_NFCT_ENABLED 0
#endif
// <o> NRFX_NFCT_CONFIG_IRQ_PRIORITY  - Interrupt priority
 
// <0=> 0 (highest) 
// <1=> 1 
// <2=> 2 
// <3=> 3 
// <4=> 4 
// <5=> 5 
// <6=> 6 
// <7=> 7 

#ifndef NRFX_NFCT_CONFIG_IRQ_PRIORITY
#define NRFX_NFCT_CONFIG_IRQ_PRIORITY 6
#endif

// <e> NRFX_NFCT_CONFIG_LOG_ENABLED - Enables logging in the module.
//==========================================================
#ifndef NRFX_NFCT_CONFIG_LOG_ENABLED
#define NRFX_NFCT_CONFIG_LOG_ENABLED 0
#endif
// <o> NRFX_NFCT_CONFIG_LOG_LEVEL  - Default Severity level
 
// <0=> Off 
// <1=> Error 
// <2=> Warning 
// <3=> Info 
// <4=> Debug 

#ifndef NRFX_NFCT_CONFIG_LOG_LEVEL
#define NRFX_NFCT_CONFIG_LOG_LEVEL 3
#endif

// <o> NRFX_NFCT_CONFIG_INFO_COLOR  - ANSI escape code prefix.
 
// <0=> Default 
// <1=> Black 
// <2=> Red 
// <3=> Green 
// <4=> Yellow 
// <5=> Blue 
// <6=> Magenta 
// <7=> Cyan 
// <8=> White 

#ifndef NRFX_NFCT_CONFIG_INFO_COLOR
#define NRFX_NFCT_CONFIG_INFO_COLOR 0
#endif

// <o> NRFX_NFCT_CONFIG_DEBUG_COLOR  - ANSI escape code prefix.
 
// <0=> Default 
// <1=> Black 
// <2=> Red 
// <3=> Green 
// <4=> Yellow 
// <5=> Blue 
// <6=> Magenta 
// <7=> Cyan 
// <8=> White 

#ifndef NRFX_NFCT_CONFIG_DEBUG_COLOR
#define NRFX_NFCT_CONFIG_DEBUG_COLOR 0
#endif

// </e>

// </e>

// <e> NRFX_PDM_ENABLED - nrfx_pdm - PDM peripheral driver
//==========================================================
#ifndef NRFX_PDM_ENABLED
#define NRFX_PDM_ENABLED 0
#endif
// <o> NRFX_PDM_CONFIG_MODE  - Mode
 
// <0=> Stereo 
// <1=> Mono 

#ifndef NRFX_PDM_CONFIG_MODE
#define NRFX_PDM_CONFIG_MODE 1
#endif

// <o> NRFX_PDM_CONFIG_EDGE  - Edge
 
// <0=> Left falling 
// <1=> Left rising 

#ifndef NRFX_PDM_CONFIG_EDGE
#define NRFX_PDM_CONFIG_EDGE 0
#endif

// <o> NRFX_PDM_CONFIG_CLOCK_FREQ  - Clock frequency
 
// <134217728=> 1000k 
// <138412032=> 1032k (default) 
// <142606336=> 1067k 

#ifndef NRFX_PDM_CONFIG_CLOCK_FREQ
#define NRFX_PDM_CONFIG_CLOCK_FREQ 138412032
#endif

// <o> NRFX_PDM_CONFIG_IRQ_PRIORITY  - Interrupt priority
 
// <0=> 0 (highest) 
// <1=> 1 
// <2=> 2 
// <3=> 3 
// <4=> 4 
// <5=> 5 
// <6=> 6 
// <7=> 7 

#ifndef NRFX_PDM_CONFIG_IRQ_PRIORITY
#define NRFX_PDM_CONFIG_IRQ_PRIORITY 6
#endif

// <e> NRFX_PDM_CONFIG_LOG_ENABLED - Enables logging in the module.
//==========================================================
#ifndef NRFX_PDM_CONFIG_LOG_ENABLED
#define NRFX_PDM_CONFIG_LOG_ENABLED 0
#endif
// <o> NRFX_PDM_CONFIG_LOG_LEVEL  - Default Severity level
 
// <0=> Off 
// <1=> Error 
// <2=> Warning 
// <3=> Info 
// <4=> Debug 

#ifndef NRFX_PDM_CONFIG_LOG_LEVEL
#define NRFX_PDM_CONFIG_LOG_LEVEL 3
#endif

// <o> NRFX_PDM_CONFIG_INFO_COLOR  - ANSI escape code prefix.
 
// <0=> Default 
// <1=> Black 
// <2=> Red 
// <3=> Green 
// <4=> Yellow 
// <5=> Blue 
// <6=> Magenta 
// <7=> Cyan 
// <8=> White 

#ifndef NRFX_PDM_CONFIG_INFO_COLOR
#define NRFX_PDM_CONFIG_INFO_COLOR 0
#endif

// <o> NRFX_PDM_CONFIG_DEBUG_COLOR  - ANSI escape code prefix.
 
// <0=> Default 
// <1=> Black 
// <2=> Red 
// <3=> Green 
// <4=> Yellow 
// <5=> Blue 
// <6=> Magenta 
// <7=> Cyan 
// <8=> White 

#ifndef NRFX_PDM_CONFIG_DEBUG_COLOR
#define NRFX_PDM_CONFIG_DEBUG_COLOR 0
#endif

// </e>

// </e>

// <e> NRFX_POWER_ENABLED - nrfx_power - POWER peripheral driver
//==========================================================
#ifndef NRFX_POWER_ENABLED
#define NRFX_POWER_ENABLED 0
#endif
// <o> NRFX_POWER_CONFIG_IRQ_PRIORITY  - Interrupt priority
 
// <0=> 0 (highest) 
// <1=> 1 
// <2=> 2 
// <3=> 3 
// <4=> 4 
// <5=> 5 
// <6=> 6 
// <7=> 7 

#ifndef NRFX_POWER_CONFIG_IRQ_PRIORITY
#define NRFX_POWER_CONFIG_IRQ_PRIORITY 6
#endif

// <q> NRFX_POWER_CONFIG_DEFAULT_DCDCEN  - The default configuration of main DCDC regulator
 

// <i> This settings means only that components for DCDC regulator are installed and it can be enabled.

#ifndef NRFX_POWER_CONFIG_DEFAULT_DCDCEN
#define NRFX_POWER_CONFIG_DEFAULT_DCDCEN 0
#endif

// <q> NRFX_POWER_CONFIG_DEFAULT_DCDCENHV  - The default configuration of High Voltage DCDC regulator
 

// <i> This settings means only that components for DCDC regulator are installed and it can be enabled.

#ifndef NRFX_POWER_CONFIG_DEFAULT_DCDCENHV
#define NRFX_POWER_CONFIG_DEFAULT_DCDCENHV 0
#endif

// </e>

// <e> NRFX_PPI_ENABLED - nrfx_ppi - PPI peripheral allocator
//==========================================================
#ifndef NRFX_PPI_ENABLED
#define NRFX_PPI_ENABLED 0
#endif
// <e> NRFX_PPI_CONFIG_LOG_ENABLED - Enables logging in the module.
//==========================================================
#ifndef NRFX_PPI_CONFIG_LOG_ENABLED
#define NRFX_PPI_CONFIG_LOG_ENABLED 0
#endif
// <o> NRFX_PPI_CONFIG_LOG_LEVEL  - Default Severity level
 
// <0=> Off 
// <1=> Error 
// <2=> Warning 
// <3=> Info 
// <4=> Debug 

#ifndef NRFX_PPI_CONFIG_LOG_LEVEL
#define NRFX_PPI_CONFIG_LOG_LEVEL 3
#endif

// <o> NRFX_PPI_CONFIG_INFO_COLOR  - ANSI escape code prefix.
 
// <0=> Default 
// <1=> Black 
// <2=> Red 
// <3=> Green 
// <4=> Yellow 
// <5=> Blue 
// <6=> Magenta 
// <7=> Cyan 
// <8=> White 

#ifndef NRFX_PPI_CONFIG_INFO_COLOR
#define NRFX_PPI_CONFIG_INFO_COLOR 0
#endif

// <o> NRFX_PPI_CONFIG_DEBUG_COLOR  - ANSI escape code prefix.
 
// <0=> Default 
// <1=> Black 
// <2=> Red 
// <3=> Green 
// <4=> Yellow 
// <5=> Blue 
// <6=> Magenta 
// <7=> Cyan 
// <8=> White 

#ifndef NRFX_PPI_CONFIG_DEBUG_COLOR
#define NRFX_PPI_CONFIG_DEBUG_COLOR 0
#endif

// </e>

// </e>

// <e> NRFX_PRS_ENABLED - nrfx_prs - Peripheral Resource Sharing module
//==========================================================
#ifndef NRFX_PRS_ENABLED
#define NRFX_PRS_ENABLED 1
#endif
// <q> NRFX_PRS_BOX_0_ENABLED  - Enables box 0 in the module.
 

#ifndef NRFX_PRS_BOX_0_ENABLED
#define NRFX_PRS_BOX_0_ENABLED 0
#endif

// <q> NRFX_PRS_BOX_1_ENABLED  - Enables box 1 in the module.
 

#ifndef NRFX_PRS_BOX_1_ENABLED
#define NRFX_PRS_BOX_1_ENABLED 0
#endif

// <q> NRFX_PRS_BOX_2_ENABLED  - Enables box 2 in the module.
 

#ifndef NRFX_PRS_BOX_2_ENABLED
#define NRFX_PRS_BOX_2_ENABLED 0
#endif

// <q> NRFX_PRS_BOX_3_ENABLED  - Enables box 3 in the module.
 

#ifndef NRFX_PRS_BOX_3_ENABLED
#define NRFX_PRS_BOX_3_ENABLED 0
#endif

// <q> NRFX_PRS_BOX_4_ENABLED  - Enables box 4 in the module.
 

#ifndef NRFX_PRS_BOX_4_ENABLED
#define NRFX_PRS_BOX_4_ENABLED 1
#endif

// <e> NRFX_PRS_CONFIG_LOG_ENABLED - Enables logging in the module.
//==========================================================
#ifndef NRFX_PRS_CONFIG_LOG_ENABLED
#define NRFX_PRS_CONFIG_LOG_ENABLED 0
#endif
// <o> NRFX_PRS_CONFIG_LOG_LEVEL  - Default Severity level
 
// <0=> Off 
// <1=> Error 
// <2=> Warning 
// <3=> Info 
// <4=> Debug 

#ifndef NRFX_PRS_CONFIG_LOG_LEVEL
#define NRFX_PRS_CONFIG_LOG_LEVEL 3
#endif

// <o> NRFX_PRS_CONFIG_INFO_COLOR  - ANSI escape code prefix.
 
// <0=> Default 
// <1=> Black 
// <2=> Red 
// <3=> Green 
// <4=> Yellow 
// <5=> Blue 
// <6=> Magenta 
// <7=> Cyan 
// <8=> White 

#ifndef NRFX_PRS_CONFIG_INFO_COLOR
#define NRFX_PRS_CONFIG_INFO_COLOR 0
#endif

// <o> NRFX_PRS_CONFIG_DEBUG_COLOR  - ANSI escape code prefix.
 
// <0=> Default 
// <1=> Black 
// <2=> Red 
// <3=> Green 
// <4=> Yellow 
// <5=> Blue 
// <6=> Magenta 
// <7=> Cyan 
// <8=> White 

#ifndef NRFX_PRS_CONFIG_DEBUG_COLOR
#define NRFX_PRS_CONFIG_DEBUG_COLOR 0
#endif

// </e>

// </e>

// <e> NRFX_PWM_ENABLED - nrfx_pwm - PWM peripheral driver
//==========================================================
#ifndef NRFX_PWM_ENABLED
#define NRFX_PWM_ENABLED 0
#endif
// <q> NRFX_PWM0_ENABLED  - Enable PWM0 instance
 

#ifndef NRFX_PWM0_ENABLED
#define NRFX_PWM0_ENABLED 0
#endif

// <q> NRFX_PWM1_ENABLED  - Enable PWM1 instance
 

#ifndef NRFX_PWM1_ENABLED
#define NRFX_PWM1_ENABLED 0
#endif

// <q> NRFX_PWM2_ENABLED  - Enable PWM2 instance
 

#ifndef NRFX_PWM2_ENABLED
#define NRFX_PWM2_ENABLED 0
#endif

// <q> NRFX_PWM3_ENABLED  - Enable PWM3 instance
 

#ifndef NRFX_PWM3_ENABLED
#define NRFX_PWM3_ENABLED 0
#endif

// <o> NRFX_PWM_DEFAULT_CONFIG_OUT0_PIN - Out0 pin  <0-31> 


#ifndef NRFX_PWM_DEFAULT_CONFIG_OUT0_PIN
#define NRFX_PWM_DEFAULT_CONFIG_OUT0_PIN 31
#endif

// <o> NRFX_PWM_DEFAULT_CONFIG_OUT1_PIN - Out1 pin  <0-31> 


#ifndef NRFX_PWM_DEFAULT_CONFIG_OUT1_PIN
#define NRFX_PWM_DEFAULT_CONFIG_OUT1_PIN 31
#endif

// <o> NRFX_PWM_DEFAULT_CONFIG_OUT2_PIN - Out2 pin  <0-31> 


#ifndef NRFX_PWM_DEFAULT_CONFIG_OUT2_PIN
#define NRFX_PWM_DEFAULT_CONFIG_OUT2_PIN 31
#endif

// <o> NRFX_PWM_DEFAULT_CONFIG_OUT3_PIN - Out3 pin  <0-31> 


#ifndef NRFX_PWM_DEFAULT_CONFIG_OUT3_PIN
#define NRFX_PWM_DEFAULT_CONFIG_OUT3_PIN 31
#endif

// <o> NRFX_PWM_DEFAULT_CONFIG_BASE_CLOCK  - Base clock
 
// <0=> 16 MHz 
// <1=> 8 MHz 
// <2=> 4 MHz 
// <3=> 2 MHz 
// <4=> 1 MHz 
// <5=> 500 kHz 
// <6=> 250 kHz 
// <7=> 125 kHz 

#ifndef NRFX_PWM_DEFAULT_CONFIG_BASE_CLOCK
#define NRFX_PWM_DEFAULT_CONFIG_BASE_CLOCK 4
#endif

// <o> NRFX_PWM_DEFAULT_CONFIG_COUNT_MODE  - Count mode
 
// <0=> Up 
// <1=> Up and Down 

#ifndef NRFX_PWM_DEFAULT_CONFIG_COUNT_MODE
#define NRFX_PWM_DEFAULT_CONFIG_COUNT_MODE 0
#endif

// <o> NRFX_PWM_DEFAULT_CONFIG_TOP_VALUE - Top value 
#ifndef NRFX_PWM_DEFAULT_CONFIG_TOP_VALUE
#define NRFX_PWM_DEFAULT_CONFIG_TOP_VALUE 1000
#endif

// <o> NRFX_PWM_DEFAULT_CONFIG_LOAD_MODE  - Load mode
 
// <0=> Common 
// <1=> Grouped 
// <2=> Individual 
// <3=> Waveform 

#ifndef NRFX_PWM_DEFAULT_CONFIG_LOAD_MODE
#define NRFX_PWM_DEFAULT_CONFIG_LOAD_MODE 0
#endif

// <o> NRFX_PWM_DEFAULT_CONFIG_STEP_MODE  - Step mode
 
// <0=> Auto 
// <1=> Triggered 

#ifndef NRFX_PWM_DEFAULT_CONFIG_STEP_MODE
#define NRFX_PWM_DEFAULT_CONFIG_STEP_MODE 0
#endif

// <o> NRFX_PWM_DEFAULT_CONFIG_IRQ_PRIORITY  - Interrupt priority
 
// <0=> 0 (highest) 
// <1=> 1 
// <2=> 2 
// <3=> 3 
// <4=> 4 
// <5=> 5 
// <6=> 6 
// <7=> 7 

#ifndef NRFX_PWM_DEFAULT_CONFIG_IRQ_PRIORITY
#define NRFX_PWM_DEFAULT_CONFIG_IRQ_PRIORITY 6
#endif

// <e> NRFX_PWM_CONFIG_LOG_ENABLED - Enables logging in the module.
//==========================================================
#ifndef NRFX_PWM_CONFIG_LOG_ENABLED
#define NRFX_PWM_CONFIG_LOG_ENABLED 0
#endif
// <o> NRFX_PWM_CONFIG_LOG_LEVEL  - Default Severity level
 
// <0=> Off 
// <1=> Error 
// <2=> Warning 
// <3=> Info 
// <4=> Debug 

#ifndef NRFX_PWM_CONFIG_LOG_LEVEL
#define NRFX_PWM_CONFIG_LOG_LEVEL 3
#endif

// <o> NRFX_PWM_CONFIG_INFO_COLOR  - ANSI escape code prefix.
 
// <0=> Default 
// <1=> Black 
// <2=> Red 
// <3=> Green 
// <4=> Yellow 
// <5=> Blue 
// <6=> Magenta 
// <7=> Cyan 
// <8=> White 

#ifndef NRFX_PWM_CONFIG_INFO_COLOR
#define NRFX_PWM_CONFIG_INFO_COLOR 0
#endif

// <o> NRFX_PWM_CONFIG_DEBUG_COLOR  - ANSI escape code prefix.
 
// <0=> Default 
// <1=> Black 
// <2=> Red 
// <3=> Green 
// <4=> Yellow 
// <5=> Blue 
// <6=> Magenta 
// <7=> Cyan 
// <8=> White 

#ifndef NRFX_PWM_CONFIG_DEBUG_COLOR
#define NRFX_PWM_CONFIG_DEBUG_COLOR 0
#endif

// </e>

// </e>

// <e> NRFX_QDEC_ENABLED - nrfx_qdec - QDEC peripheral driver
//==========================================================
#ifndef NRFX_QDEC_ENABLED
#define NRFX_QDEC_ENABLED 0
#endif
// <o> NRFX_QDEC_CONFIG_REPORTPER  - Report period
 
// <0=> 10 Samples 
// <1=> 40 Samples 
// <2=> 80 Samples 
// <3=> 120 Samples 
// <4=> 160 Samples 
// <5=> 200 Samples 
// <6=> 240 Samples 
// <7=> 280 Samples 

#ifndef NRFX_QDEC_CONFIG_REPORTPER
#define NRFX_QDEC_CONFIG_REPORTPER 0
#endif

// <o> NRFX_QDEC_CONFIG_SAMPLEPER  - Sample period
 
// <0=> 128 us 
// <1=> 256 us 
// <2=> 512 us 
// <3=> 1024 us 
// <4=> 2048 us 
// <5=> 4096 us 
// <6=> 8192 us 
// <7=> 16384 us 

#ifndef NRFX_QDEC_CONFIG_SAMPLEPER
#define NRFX_QDEC_CONFIG_SAMPLEPER 7
#endif

// <o> NRFX_QDEC_CONFIG_PIO_A - A pin  <0-31> 


#ifndef NRFX_QDEC_CONFIG_PIO_A
#define NRFX_QDEC_CONFIG_PIO_A 31
#endif

// <o> NRFX_QDEC_CONFIG_PIO_B - B pin  <0-31> 


#ifndef NRFX_QDEC_CONFIG_PIO_B
#define NRFX_QDEC_CONFIG_PIO_B 31
#endif

// <o> NRFX_QDEC_CONFIG_PIO_LED - LED pin  <0-31> 


#ifndef NRFX_QDEC_CONFIG_PIO_LED
#define NRFX_QDEC_CONFIG_PIO_LED 31
#endif

// <o> NRFX_QDEC_CONFIG_LEDPRE - LED pre 
#ifndef NRFX_QDEC_CONFIG_LEDPRE
#define NRFX_QDEC_CONFIG_LEDPRE 511
#endif

// <o> NRFX_QDEC_CONFIG_LEDPOL  - LED polarity
 
// <0=> Active low 
// <1=> Active high 

#ifndef NRFX_QDEC_CONFIG_LEDPOL
#define NRFX_QDEC_CONFIG_LEDPOL 1
#endif

// <q> NRFX_QDEC_CONFIG_DBFEN  - Debouncing enable
 

#ifndef NRFX_QDEC_CONFIG_DBFEN
#define NRFX_QDEC_CONFIG_DBFEN 0
#endif

// <q> NRFX_QDEC_CONFIG_SAMPLE_INTEN  - Sample ready interrupt enable
 

#ifndef NRFX_QDEC_CONFIG_SAMPLE_INTEN
#define NRFX_QDEC_CONFIG_SAMPLE_INTEN 0
#endif

// <o> NRFX_QDEC_CONFIG_IRQ_PRIORITY  - Interrupt priority
 
// <0=> 0 (highest) 
// <1=> 1 
// <2=> 2 
// <3=> 3 
// <4=> 4 
// <5=> 5 
// <6=> 6 
// <7=> 7 

#ifndef NRFX_QDEC_CONFIG_IRQ_PRIORITY
#define NRFX_QDEC_CONFIG_IRQ_PRIORITY 6
#endif

// <e> NRFX_QDEC_CONFIG_LOG_ENABLED - Enables logging in the module.
//==========================================================
#ifndef NRFX_QDEC_CONFIG_LOG_ENABLED
#define NRFX_QDEC_CONFIG_LOG_ENABLED 0
#endif
// <o> NRFX_QDEC_CONFIG_LOG_LEVEL  - Default Severity level
 
// <0=> Off 
// <1=> Error 
// <2=> Warning 
// <3=> Info 
// <4=> Debug 

#ifndef NRFX_QDEC_CONFIG_LOG_LEVEL
#define NRFX_QDEC_CONFIG_LOG_LEVEL 3
#endif

// <o> NRFX_QDEC_CONFIG_INFO_COLOR  - ANSI escape code prefix.
 
// <0=> Default 
// <1=> Black 
// <2=> Red 
// <3=> Green 
// <4=> Yellow 
// <5=> Blue 
// <6=> Magenta 
// <7=> Cyan 
// <8=> White 

#ifndef NRFX_QDEC_CONFIG_INFO_COLOR
#define NRFX_QDEC_CONFIG_INFO_COLOR 0
#endif

// <o> NRFX_QDEC_CONFIG_DEBUG_COLOR  - ANSI escape code prefix.
 
// <0=> Default 
// <1=> Black 
// <2=> Red 
// <3=> Green 
// <4=> Yellow 
// <5=> Blue 
// <6=> Magenta 
// <7=> Cyan 
// <8=> White 

#ifndef NRFX_QDEC_CONFIG_DEBUG_COLOR
#define NRFX_QDEC_CONFIG_DEBUG_COLOR 0
#endif

// </e>

// </e>

// <e> NRFX_QSPI_ENABLED - nrfx_qspi - QSPI peripheral driver
//==========================================================
#ifndef NRFX_QSPI_ENABLED
#define NRFX_QSPI_ENABLED 0
#endif
// <o> NRFX_QSPI_CONFIG_SCK_DELAY - tSHSL, tWHSL and tSHWL in number of 16 MHz periods (62.5 ns).  <0-255> 


#ifndef NRFX_QSPI_CONFIG_SCK_DELAY
#define NRFX_QSPI_CONFIG_SCK_DELAY 1
#endif

// <o> NRFX_QSPI_CONFIG_XIP_OFFSET - Address offset in the external memory for Execute in Place operation. 
#ifndef NRFX_QSPI_CONFIG_XIP_OFFSET
#define NRFX_QSPI_CONFIG_XIP_OFFSET 0
#endif

// <o> NRFX_QSPI_CONFIG_READOC  - Number of data lines and opcode used for reading.
 
// <0=> FastRead 
// <1=> Read2O 
// <2=> Read2IO 
// <3=> Read4O 
// <4=> Read4IO 

#ifndef NRFX_QSPI_CONFIG_READOC
#define NRFX_QSPI_CONFIG_READOC 0
#endif

// <o> NRFX_QSPI_CONFIG_WRITEOC  - Number of data lines and opcode used for writing.
 
// <0=> PP 
// <1=> PP2O 
// <2=> PP4O 
// <3=> PP4IO 

#ifndef NRFX_QSPI_CONFIG_WRITEOC
#define NRFX_QSPI_CONFIG_WRITEOC 0
#endif

// <o> NRFX_QSPI_CONFIG_ADDRMODE  - Addressing mode.
 
// <0=> 24bit 
// <1=> 32bit 

#ifndef NRFX_QSPI_CONFIG_ADDRMODE
#define NRFX_QSPI_CONFIG_ADDRMODE 0
#endif

// <o> NRFX_QSPI_CONFIG_MODE  - SPI mode.
 
// <0=> Mode 0 
// <1=> Mode 1 

#ifndef NRFX_QSPI_CONFIG_MODE
#define NRFX_QSPI_CONFIG_MODE 0
#endif

// <o> NRFX_QSPI_CONFIG_FREQUENCY  - Frequency divider.
 
// <0=> 32MHz/1 
// <1=> 32MHz/2 
// <2=> 32MHz/3 
// <3=> 32MHz/4 
// <4=> 32MHz/5 
// <5=> 32MHz/6 
// <6=> 32MHz/7 
// <7=> 32MHz/8 
// <8=> 32MHz/9 
// <9=> 32MHz/10 
// <10=> 32MHz/11 
// <11=> 32MHz/12 
// <12=> 32MHz/13 
// <13=> 32MHz/14 
// <14=> 32MHz/15 
// <15=> 32MHz/16 

#ifndef NRFX_QSPI_CONFIG_FREQUENCY
#define NRFX_QSPI_CONFIG_FREQUENCY 15
#endif

// <s> NRFX_QSPI_PIN_SCK - SCK pin value.
#ifndef NRFX_QSPI_PIN_SCK
#define NRFX_QSPI_PIN_SCK NRF_QSPI_PIN_NOT_CONNECTED
#endif

// <s> NRFX_QSPI_PIN_CSN - CSN pin value.
#ifndef NRFX_QSPI_PIN_CSN
#define NRFX_QSPI_PIN_CSN NRF_QSPI_PIN_NOT_CONNECTED
#endif

// <s> NRFX_QSPI_PIN_IO0 - IO0 pin value.
#ifndef NRFX_QSPI_PIN_IO0
#define NRFX_QSPI_PIN_IO0 NRF_QSPI_PIN_NOT_CONNECTED
#endif

// <s> NRFX_QSPI_PIN_IO1 - IO1 pin value.
#ifndef NRFX_QSPI_PIN_IO1
#define NRFX_QSPI_PIN_IO1 NRF_QSPI_PIN_NOT_CONNECTED
#endif

// <s> NRFX_QSPI_PIN_IO2 - IO2 pin value.
#ifndef NRFX_QSPI_PIN_IO2
#define NRFX_QSPI_PIN_IO2 NRF_QSPI_PIN_NOT_CONNECTED
#endif

// <s> NRFX_QSPI_PIN_IO3 - IO3 pin value.
#ifndef NRFX_QSPI_PIN_IO3
#define NRFX_QSPI_PIN_IO3 NRF_QSPI_PIN_NOT_CONNECTED
#endif

// <o> NRFX_QSPI_CONFIG_IRQ_PRIORITY  - Interrupt priority
 
// <0=> 0 (highest) 
// <1=> 1 
// <2=> 2 
// <3=> 3 
// <4=> 4 
// <5=> 5 
// <6=> 6 
// <7=> 7 

#ifndef NRFX_QSPI_CONFIG_IRQ_PRIORITY
#define NRFX_QSPI_CONFIG_IRQ_PRIORITY 6
#endif

// </e>

// <e> NRFX_RNG_ENABLED - nrfx_rng - RNG peripheral driver
//==========================================================
#ifndef NRFX_RNG_ENABLED
#define NRFX_RNG_ENABLED 0
#endif
// <q> NRFX_RNG_CONFIG_ERROR_CORRECTION  - Error correction
 

#ifndef NRFX_RNG_CONFIG_ERROR_CORRECTION
#define NRFX_RNG_CONFIG_ERROR_CORRECTION 1
#endif

// <o> NRFX_RNG_CONFIG_IRQ_PRIORITY  - Interrupt priority
 
// <0=> 0 (highest) 
// <1=> 1 
// <2=> 2 
// <3=> 3 
// <4=> 4 
// <5=> 5 
// <6=> 6 
// <7=> 7 

#ifndef NRFX_RNG_CONFIG_IRQ_PRIORITY
#define NRFX_RNG_CONFIG_IRQ_PRIORITY 6
#endif

// <e> NRFX_RNG_CONFIG_LOG_ENABLED - Enables logging in the module.
//==========================================================
#ifndef NRFX_RNG_CONFIG_LOG_ENABLED
#define NRFX_RNG_CONFIG_LOG_ENABLED 0
#endif
// <o> NRFX_RNG_CONFIG_LOG_LEVEL  - Default Severity level
 
// <0=> Off 
// <1=> Error 
// <2=> Warning 
// <3=> Info 
// <4=> Debug 

#ifndef NRFX_RNG_CONFIG_LOG_LEVEL
#define NRFX_RNG_CONFIG_LOG_LEVEL 3
#endif

// <o> NRFX_RNG_CONFIG_INFO_COLOR  - ANSI escape code prefix.
 
// <0=> Default 
// <1=> Black 
// <2=> Red 
// <3=> Green 
// <4=> Yellow 
// <5=> Blue 
// <6=> Magenta 
// <7=> Cyan 
// <8=> White 

#ifndef NRFX_RNG_CONFIG_INFO_COLOR
#define NRFX_RNG_CONFIG_INFO_COLOR 0
#endif

// <o> NRFX_RNG_CONFIG_DEBUG_COLOR  - ANSI escape code prefix.
 
// <0=> Default 
// <1=> Black 
// <2=> Red 
// <3=> Green 
// <4=> Yellow 
// <5=> Blue 
// <6=> Magenta 
// <7=> Cyan 
// <8=> White 

#ifndef NRFX_RNG_CONFIG_DEBUG_COLOR
#define NRFX_RNG_CONFIG_DEBUG_COLOR 0
#endif

// </e>

// </e>

// <e> NRFX_RTC_ENABLED - nrfx_rtc - RTC peripheral driver
//==========================================================
#ifndef NRFX_RTC_ENABLED
#define NRFX_RTC_ENABLED 0
#endif
// <q> NRFX_RTC0_ENABLED  - Enable RTC0 instance
 

#ifndef NRFX_RTC0_ENABLED
#define NRFX_RTC0_ENABLED 0
#endif

// <q> NRFX_RTC1_ENABLED  - Enable RTC1 instance
 

#ifndef NRFX_RTC1_ENABLED
#define NRFX_RTC1_ENABLED 0
#endif

// <q> NRFX_RTC2_ENABLED  - Enable RTC2 instance
 

#ifndef NRFX_RTC2_ENABLED
#define NRFX_RTC2_ENABLED 0
#endif

// <o> NRFX_RTC_MAXIMUM_LATENCY_US - Maximum possible time[us] in highest priority interrupt 
#ifndef NRFX_RTC_MAXIMUM_LATENCY_US
#define NRFX_RTC_MAXIMUM_LATENCY_US 2000
#endif

// <o> NRFX_RTC_DEFAULT_CONFIG_FREQUENCY - Frequency  <16-32768> 


#ifndef NRFX_RTC_DEFAULT_CONFIG_FREQUENCY
#define NRFX_RTC_DEFAULT_CONFIG_FREQUENCY 32768
#endif

// <q> NRFX_RTC_DEFAULT_CONFIG_RELIABLE  - Ensures safe compare event triggering
 

#ifndef NRFX_RTC_DEFAULT_CONFIG_RELIABLE
#define NRFX_RTC_DEFAULT_CONFIG_RELIABLE 0
#endif

// <o> NRFX_RTC_DEFAULT_CONFIG_IRQ_PRIORITY  - Interrupt priority
 
// <0=> 0 (highest) 
// <1=> 1 
// <2=> 2 
// <3=> 3 
// <4=> 4 
// <5=> 5 
// <6=> 6 
// <7=> 7 

#ifndef NRFX_RTC_DEFAULT_CONFIG_IRQ_PRIORITY
#define NRFX_RTC_DEFAULT_CONFIG_IRQ_PRIORITY 6
#endif

// <e> NRFX_RTC_CONFIG_LOG_ENABLED - Enables logging in the module.
//==========================================================
#ifndef NRFX_RTC_CONFIG_LOG_ENABLED
#define NRFX_RTC_CONFIG_LOG_ENABLED 0
#endif
// <o> NRFX_RTC_CONFIG_LOG_LEVEL  - Default Severity level
 
// <0=> Off 
// <1=> Error 
// <2=> Warning 
// <3=> Info 
// <4=> Debug 

#ifndef NRFX_RTC_CONFIG_LOG_LEVEL
#define NRFX_RTC_CONFIG_LOG_LEVEL 3
#endif

// <o> NRFX_RTC_CONFIG_INFO_COLOR  - ANSI escape code prefix.
 
// <0=> Default 
// <1=> Black 
// <2=> Red 
// <3=> Green 
// <4=> Yellow 
// <5=> Blue 
// <6=> Magenta 
// <7=> Cyan 
// <8=> White 

#ifndef NRFX_RTC_CONFIG_INFO_COLOR
#define NRFX_RTC_CONFIG_INFO_COLOR 0
#endif

// <o> NRFX_RTC_CONFIG_DEBUG_COLOR  - ANSI escape code prefix.
 
// <0=> Default 
// <1=> Black 
// <2=> Red 
// <3=> Green 
// <4=> Yellow 
// <5=> Blue 
// <6=> Magenta 
// <7=> Cyan 
// <8=> White 

#ifndef NRFX_RTC_CONFIG_DEBUG_COLOR
#define NRFX_RTC_CONFIG_DEBUG_COLOR 0
#endif

// </e>

// </e>

// <e> NRFX_SAADC_ENABLED - nrfx_saadc - SAADC peripheral driver
//==========================================================
#ifndef NRFX_SAADC_ENABLED
#define NRFX_SAADC_ENABLED 0
#endif
// <o> NRFX_SAADC_CONFIG_RESOLUTION  - Resolution
 
// <0=> 8 bit 
// <1=> 10 bit 
// <2=> 12 bit 
// <3=> 14 bit 

#ifndef NRFX_SAADC_CONFIG_RESOLUTION
#define NRFX_SAADC_CONFIG_RESOLUTION 1
#endif

// <o> NRFX_SAADC_CONFIG_OVERSAMPLE  - Sample period
 
// <0=> Disabled 
// <1=> 2x 
// <2=> 4x 
// <3=> 8x 
// <4=> 16x 
// <5=> 32x 
// <6=> 64x 
// <7=> 128x 
// <8=> 256x 

#ifndef NRFX_SAADC_CONFIG_OVERSAMPLE
#define NRFX_SAADC_CONFIG_OVERSAMPLE 0
#endif

// <q> NRFX_SAADC_CONFIG_LP_MODE  - Enabling low power mode
 

#ifndef NRFX_SAADC_CONFIG_LP_MODE
#define NRFX_SAADC_CONFIG_LP_MODE 0
#endif

// <o> NRFX_SAADC_CONFIG_IRQ_PRIORITY  - Interrupt priority
 
// <0=> 0 (highest) 
// <1=> 1 
// <2=> 2 
// <3=> 3 
// <4=> 4 
// <5=> 5 
// <6=> 6 
// <7=> 7 

#ifndef NRFX_SAADC_CONFIG_IRQ_PRIORITY
#define NRFX_SAADC_CONFIG_IRQ_PRIORITY 6
#endif

// <e> NRFX_SAADC_CONFIG_LOG_ENABLED - Enables logging in the module.
//==========================================================
#ifndef NRFX_SAADC_CONFIG_LOG_ENABLED
#define NRFX_SAADC_CONFIG_LOG_ENABLED 0
#endif
// <o> NRFX_SAADC_CONFIG_LOG_LEVEL  - Default Severity level
 
// <0=> Off 
// <1=> Error 
// <2=> Warning 
// <3=> Info 
// <4=> Debug 

#ifndef NRFX_SAADC_CONFIG_LOG_LEVEL
#define NRFX_SAADC_CONFIG_LOG_LEVEL 3
#endif

// <o> NRFX_SAADC_CONFIG_INFO_COLOR  - ANSI escape code prefix.
 
// <0=> Default 
// <1=> Black 
// <2=> Red 
// <3=> Green 
// <4=> Yellow 
// <5=> Blue 
// <6=> Magenta 
// <7=> Cyan 
// <8=> White 

#ifndef NRFX_SAADC_CONFIG_INFO_COLOR
#define NRFX_SAADC_CONFIG_INFO_COLOR 0
#endif

// <o> NRFX_SAADC_CONFIG_DEBUG_COLOR  - ANSI escape code prefix.
 
// <0=> Default 
// <1=> Black 
// <2=> Red 
// <3=> Green 
// <4=> Yellow 
// <5=> Blue 
// <6=> Magenta 
// <7=> Cyan 
// <8=> White 

#ifndef NRFX_SAADC_CONFIG_DEBUG_COLOR
#define NRFX_SAADC_CONFIG_DEBUG_COLOR 0
#endif

// </e>

// </e>

// <e> NRFX_SPIM_ENABLED - nrfx_spim - SPIM peripheral driver
//==========================================================
#ifndef NRFX_SPIM_ENABLED
#define NRFX_SPIM_ENABLED 0
#endif
// <q> NRFX_SPIM0_ENABLED  - Enable SPIM0 instance
 

#ifndef NRFX_SPIM0_ENABLED
#define NRFX_SPIM0_ENABLED 0
#endif

// <q> NRFX_SPIM1_ENABLED  - Enable SPIM1 instance
 

#ifndef NRFX_SPIM1_ENABLED
#define NRFX_SPIM1_ENABLED 0
#endif

// <q> NRFX_SPIM2_ENABLED  - Enable SPIM2 instance
 

#ifndef NRFX_SPIM2_ENABLED
#define NRFX_SPIM2_ENABLED 0
#endif

// <q> NRFX_SPIM3_ENABLED  - Enable SPIM3 instance
 

#ifndef NRFX_SPIM3_ENABLED
#define NRFX_SPIM3_ENABLED 0
#endif

// <q> NRFX_SPIM_EXTENDED_ENABLED  - Enable extended SPIM features
 

#ifndef NRFX_SPIM_EXTENDED_ENABLED
#define NRFX_SPIM_EXTENDED_ENABLED 0
#endif

// <o> NRFX_SPIM_MISO_PULL_CFG  - MISO pin pull configuration.
 
// <0=> NRF_GPIO_PIN_NOPULL 
// <1=> NRF_GPIO_PIN_PULLDOWN 
// <3=> NRF_GPIO_PIN_PULLUP 

#ifndef NRFX_SPIM_MISO_PULL_CFG
#define NRFX_SPIM_MISO_PULL_CFG 1
#endif

// <o> NRFX_SPIM_DEFAULT_CONFIG_IRQ_PRIORITY  - Interrupt priority
 
// <0=> 0 (highest) 
// <1=> 1 
// <2=> 2 
// <3=> 3 
// <4=> 4 
// <5=> 5 
// <6=> 6 
// <7=> 7 

#ifndef NRFX_SPIM_DEFAULT_CONFIG_IRQ_PRIORITY
#define NRFX_SPIM_DEFAULT_CONFIG_IRQ_PRIORITY 6
#endif

// <e> NRFX_SPIM_CONFIG_LOG_ENABLED - Enables logging in the module.
//==========================================================
#ifndef NRFX_SPIM_CONFIG_LOG_ENABLED
#define NRFX_SPIM_CONFIG_LOG_ENABLED 0
#endif
// <o> NRFX_SPIM_CONFIG_LOG_LEVEL  - Default Severity level
 
// <0=> Off 
// <1=> Error 
// <2=> Warning 
// <3=> Info 
// <4=> Debug 

#ifndef NRFX_SPIM_CONFIG_LOG_LEVEL
#define NRFX_SPIM_CONFIG_LOG_LEVEL 3
#endif

// <o> NRFX_SPIM_CONFIG_INFO_COLOR  - ANSI escape code prefix.
 
// <0=> Default 
// <1=> Black 
// <2=> Red 
// <3=> Green 
// <4=> Yellow 
// <5=> Blue 
// <6=> Magenta 
// <7=> Cyan 
// <8=> White 

#ifndef NRFX_SPIM_CONFIG_INFO_COLOR
#define NRFX_SPIM_CONFIG_INFO_COLOR 0
#endif

// <o> NRFX_SPIM_CONFIG_DEBUG_COLOR  - ANSI escape code prefix.
 
// <0=> Default 
// <1=> Black 
// <2=> Red 
// <3=> Green 
// <4=> Yellow 
// <5=> Blue 
// <6=> Magenta 
// <7=> Cyan 
// <8=> White 

#ifndef NRFX_SPIM_CONFIG_DEBUG_COLOR
#define NRFX_SPIM_CONFIG_DEBUG_COLOR 0
#endif

// </e>

// </e>

// <e> NRFX_SPIS_ENABLED - nrfx_spis - SPIS peripheral driver
//==========================================================
#ifndef NRFX_SPIS_ENABLED
#define NRFX_SPIS_ENABLED 0
#endif
// <q> NRFX_SPIS0_ENABLED  - Enable SPIS0 instance
 

#ifndef NRFX_SPIS0_ENABLED
#define NRFX_SPIS0_ENABLED 0
#endif

// <q> NRFX_SPIS1_ENABLED  - Enable SPIS1 instance
 

#ifndef NRFX_SPIS1_ENABLED
#define NRFX_SPIS1_ENABLED 0
#endif

// <q> NRFX_SPIS2_ENABLED  - Enable SPIS2 instance
 

#ifndef NRFX_SPIS2_ENABLED
#define NRFX_SPIS2_ENABLED 0
#endif

// <o> NRFX_SPIS_DEFAULT_CONFIG_IRQ_PRIORITY  - Interrupt priority
 
// <0=> 0 (highest) 
// <1=> 1 
// <2=> 2 
// <3=> 3 
// <4=> 4 
// <5=> 5 
// <6=> 6 
// <7=> 7 

#ifndef NRFX_SPIS_DEFAULT_CONFIG_IRQ_PRIORITY
#define NRFX_SPIS_DEFAULT_CONFIG_IRQ_PRIORITY 6
#endif

// <o> NRFX_SPIS_DEFAULT_DEF - SPIS default DEF character  <0-255> 


#ifndef NRFX_SPIS_DEFAULT_DEF
#define NRFX_SPIS_DEFAULT_DEF 255
#endif

// <o> NRFX_SPIS_DEFAULT_ORC - SPIS default ORC character  <0-255> 


#ifndef NRFX_SPIS_DEFAULT_ORC
#define NRFX_SPIS_DEFAULT_ORC 255
#endif

// <e> NRFX_SPIS_CONFIG_LOG_ENABLED - Enables logging in the module.
//==========================================================
#ifndef NRFX_SPIS_CONFIG_LOG_ENABLED
#define NRFX_SPIS_CONFIG_LOG_ENABLED 0
#endif
// <o> NRFX_SPIS_CONFIG_LOG_LEVEL  - Default Severity level
 
// <0=> Off 
// <1=> Error 
// <2=> Warning 
// <3=> Info 
// <4=> Debug 

#ifndef NRFX_SPIS_CONFIG_LOG_LEVEL
#define NRFX_SPIS_CONFIG_LOG_LEVEL 3
#endif

// <o> NRFX_SPIS_CONFIG_INFO_COLOR  - ANSI escape code prefix.
 
// <0=> Default 
// <1=> Black 
// <2=> Red 
// <3=> Green 
// <4=> Yellow 
// <5=> Blue 
// <6=> Magenta 
// <7=> Cyan 
// <8=> White 

#ifndef NRFX_SPIS_CONFIG_INFO_COLOR
#define NRFX_SPIS_CONFIG_INFO_COLOR 0
#endif

// <o> NRFX_SPIS_CONFIG_DEBUG_COLOR  - ANSI escape code prefix.
 
// <0=> Default 
// <1=> Black 
// <2=> Red 
// <3=> Green 
// <4=> Yellow 
// <5=> Blue 
// <6=> Magenta 
// <7=> Cyan 
// <8=> White 

#ifndef NRFX_SPIS_CONFIG_DEBUG_COLOR
#define NRFX_SPIS_CONFIG_DEBUG_COLOR 0
#endif

// </e>

// </e>

// <e> NRFX_SPI_ENABLED - nrfx_spi - SPI peripheral driver
//==========================================================
#ifndef NRFX_SPI_ENABLED
#define NRFX_SPI_ENABLED 0
#endif
// <q> NRFX_SPI0_ENABLED  - Enable SPI0 instance
 

#ifndef NRFX_SPI0_ENABLED
#define NRFX_SPI0_ENABLED 0
#endif

// <q> NRFX_SPI1_ENABLED  - Enable SPI1 instance
 

#ifndef NRFX_SPI1_ENABLED
#define NRFX_SPI1_ENABLED 0
#endif

// <q> NRFX_SPI2_ENABLED  - Enable SPI2 instance
 

#ifndef NRFX_SPI2_ENABLED
#define NRFX_SPI2_ENABLED 0
#endif

// <o> NRFX_SPI_MISO_PULL_CFG  - MISO pin pull configuration.
 
// <0=> NRF_GPIO_PIN_NOPULL 
// <1=> NRF_GPIO_PIN_PULLDOWN 
// <3=> NRF_GPIO_PIN_PULLUP 

#ifndef NRFX_SPI_MISO_PULL_CFG
#define NRFX_SPI_MISO_PULL_CFG 1
#endif

// <o> NRFX_SPI_DEFAULT_CONFIG_IRQ_PRIORITY  - Interrupt priority
 
// <0=> 0 (highest) 
// <1=> 1 
// <2=> 2 
// <3=> 3 
// <4=> 4 
// <5=> 5 
// <6=> 6 
// <7=> 7 

#ifndef NRFX_SPI_DEFAULT_CONFIG_IRQ_PRIORITY
#define NRFX_SPI_DEFAULT_CONFIG_IRQ_PRIORITY 6
#endif

// <e> NRFX_SPI_CONFIG_LOG_ENABLED - Enables logging in the module.
//==========================================================
#ifndef NRFX_SPI_CONFIG_LOG_ENABLED
#define NRFX_SPI_CONFIG_LOG_ENABLED 0
#endif
// <o> NRFX_SPI_CONFIG_LOG_LEVEL  - Default Severity level
 
// <0=> Off 
// <1=> Error 
// <2=> Warning 
// <3=> Info 
// <4=> Debug 

#ifndef NRFX_SPI_CONFIG_LOG_LEVEL
#define NRFX_SPI_CONFIG_LOG_LEVEL 3
#endif

// <o> NRFX_SPI_CONFIG_INFO_COLOR  - ANSI escape code prefix.
 
// <0=> Default 
// <1=> Black 
// <2=> Red 
// <3=> Green 
// <4=> Yellow 
// <5=> Blue 
// <6=> Magenta 
// <7=> Cyan 
// <8=> White 

#ifndef NRFX_SPI_CONFIG_INFO_COLOR
#define NRFX_SPI_CONFIG_INFO_COLOR 0
#endif

// <o> NRFX_SPI_CONFIG_DEBUG_COLOR  - ANSI escape code prefix.
 
// <0=> Default 
// <1=> Black 
// <2=> Red 
// <3=> Green 
// <4=> Yellow 
// <5=> Blue 
// <6=> Magenta 
// <7=> Cyan 
// <8=> White 

#ifndef NRFX_SPI_CONFIG_DEBUG_COLOR
#define NRFX_SPI_CONFIG_DEBUG_COLOR 0
#endif

// </e>

// </e>

// <e> NRFX_SWI_ENABLED - nrfx_swi - SWI/EGU peripheral allocator
//==========================================================
#ifndef NRFX_SWI_ENABLED
#define NRFX_SWI_ENABLED 0
#endif
// <q> NRFX_EGU_ENABLED  - Enable EGU support
 

#ifndef NRFX_EGU_ENABLED
#define NRFX_EGU_ENABLED 0
#endif

// <q> NRFX_SWI0_DISABLED  - Exclude SWI0 from being utilized by the driver
 

#ifndef NRFX_SWI0_DISABLED
#define NRFX_SWI0_DISABLED 0
#endif

// <q> NRFX_SWI1_DISABLED  - Exclude SWI1 from being utilized by the driver
 

#ifndef NRFX_SWI1_DISABLED
#define NRFX_SWI1_DISABLED 0
#endif

// <q> NRFX_SWI2_DISABLED  - Exclude SWI2 from being utilized by the driver
 

#ifndef NRFX_SWI2_DISABLED
#define NRFX_SWI2_DISABLED 0
#endif

// <q> NRFX_SWI3_DISABLED  - Exclude SWI3 from being utilized by the driver
 

#ifndef NRFX_SWI3_DISABLED
#define NRFX_SWI3_DISABLED 0
#endif

// <q> NRFX_SWI4_DISABLED  - Exclude SWI4 from being utilized by the driver
 

#ifndef NRFX_SWI4_DISABLED
#define NRFX_SWI4_DISABLED 0
#endif

// <q> NRFX_SWI5_DISABLED  - Exclude SWI5 from being utilized by the driver
 

#ifndef NRFX_SWI5_DISABLED
#define NRFX_SWI5_DISABLED 0
#endif

// <e> NRFX_SWI_CONFIG_LOG_ENABLED - Enables logging in the module.
//==========================================================
#ifndef NRFX_SWI_CONFIG_LOG_ENABLED
#define NRFX_SWI_CONFIG_LOG_ENABLED 0
#endif
// <o> NRFX_SWI_CONFIG_LOG_LEVEL  - Default Severity level
 
// <0=> Off 
// <1=> Error 
// <2=> Warning 
// <3=> Info 
// <4=> Debug 

#ifndef NRFX_SWI_CONFIG_LOG_LEVEL
#define NRFX_SWI_CONFIG_LOG_LEVEL 3
#endif

// <o> NRFX_SWI_CONFIG_INFO_COLOR  - ANSI escape code prefix.
 
// <0=> Default 
// <1=> Black 
// <2=> Red 
// <3=> Green 
// <4=> Yellow 
// <5=> Blue 
// <6=> Magenta 
// <7=> Cyan 
// <8=> White 

#ifndef NRFX_SWI_CONFIG_INFO_COLOR
#define NRFX_SWI_CONFIG_INFO_COLOR 0
#endif

// <o> NRFX_SWI_CONFIG_DEBUG_COLOR  - ANSI escape code prefix.
 
// <0=> Default 
// <1=> Black 
// <2=> Red 
// <3=> Green 
// <4=> Yellow 
// <5=> Blue 
// <6=> Magenta 
// <7=> Cyan 
// <8=> White 

#ifndef NRFX_SWI_CONFIG_DEBUG_COLOR
#define NRFX_SWI_CONFIG_DEBUG_COLOR 0
#endif

// </e>

// </e>

// <e> NRFX_TIMER_ENABLED - nrfx_timer - TIMER periperal driver
//==========================================================
#ifndef NRFX_TIMER_ENABLED
#define NRFX_TIMER_ENABLED 0
#endif
// <q> NRFX_TIMER0_ENABLED  - Enable TIMER0 instance
 

#ifndef NRFX_TIMER0_ENABLED
#define NRFX_TIMER0_ENABLED 0
#endif

// <q> NRFX_TIMER1_ENABLED  - Enable TIMER1 instance
 

#ifndef NRFX_TIMER1_ENABLED
#define NRFX_TIMER1_ENABLED 0
#endif

// <q> NRFX_TIMER2_ENABLED  - Enable TIMER2 instance
 

#ifndef NRFX_TIMER2_ENABLED
#define NRFX_TIMER2_ENABLED 0
#endif

// <q> NRFX_TIMER3_ENABLED  - Enable TIMER3 instance
 

#ifndef NRFX_TIMER3_ENABLED
#define NRFX_TIMER3_ENABLED 0
#endif

// <q> NRFX_TIMER4_ENABLED  - Enable TIMER4 instance
 

#ifndef NRFX_TIMER4_ENABLED
#define NRFX_TIMER4_ENABLED 0
#endif

// <o> NRFX_TIMER_DEFAULT_CONFIG_FREQUENCY  - Timer frequency if in Timer mode
 
// <0=> 16 MHz 
// <1=> 8 MHz 
// <2=> 4 MHz 
// <3=> 2 MHz 
// <4=> 1 MHz 
// <5=> 500 kHz 
// <6=> 250 kHz 
// <7=> 125 kHz 
// <8=> 62.5 kHz 
// <9=> 31.25 kHz 

#ifndef NRFX_TIMER_DEFAULT_CONFIG_FREQUENCY
#define NRFX_TIMER_DEFAULT_CONFIG_FREQUENCY 0
#endif

// <o> NRFX_TIMER_DEFAULT_CONFIG_MODE  - Timer mode or operation
 
// <0=> Timer 
// <1=> Counter 

#ifndef NRFX_TIMER_DEFAULT_CONFIG_MODE
#define NRFX_TIMER_DEFAULT_CONFIG_MODE 0
#endif

// <o> NRFX_TIMER_DEFAULT_CONFIG_BIT_WIDTH  - Timer counter bit width
 
// <0=> 16 bit 
// <1=> 8 bit 
// <2=> 24 bit 
// <3=> 32 bit 

#ifndef NRFX_TIMER_DEFAULT_CONFIG_BIT_WIDTH
#define NRFX_TIMER_DEFAULT_CONFIG_BIT_WIDTH 0
#endif

// <o> NRFX_TIMER_DEFAULT_CONFIG_IRQ_PRIORITY  - Interrupt priority
 
// <0=> 0 (highest) 
// <1=> 1 
// <2=> 2 
// <3=> 3 
// <4=> 4 
// <5=> 5 
// <6=> 6 
// <7=> 7 

#ifndef NRFX_TIMER_DEFAULT_CONFIG_IRQ_PRIORITY
#define NRFX_TIMER_DEFAULT_CONFIG_IRQ_PRIORITY 6
#endif

// <e> NRFX_TIMER_CONFIG_LOG_ENABLED - Enables logging in the module.
//==========================================================
#ifndef NRFX_TIMER_CONFIG_LOG_ENABLED
#define NRFX_TIMER_CONFIG_LOG_ENABLED 0
#endif
// <o> NRFX_TIMER_CONFIG_LOG_LEVEL  - Default Severity level
 
// <0=> Off 
// <1=> Error 
// <2=> Warning 
// <3=> Info 
// <4=> Debug 

#ifndef NRFX_TIMER_CONFIG_LOG_LEVEL
#define NRFX_TIMER_CONFIG_LOG_LEVEL 3
#endif

// <o> NRFX_TIMER_CONFIG_INFO_COLOR  - ANSI escape code prefix.
 
// <0=> Default 
// <1=> Black 
// <2=> Red 
// <3=> Green 
// <4=> Yellow 
// <5=> Blue 
// <6=> Magenta 
// <7=> Cyan 
// <8=> White 

#ifndef NRFX_TIMER_CONFIG_INFO_COLOR
#define NRFX_TIMER_CONFIG_INFO_COLOR 0
#endif

// <o> NRFX_TIMER_CONFIG_DEBUG_COLOR  - ANSI escape code prefix.
 
// <0=> Default 
// <1=> Black 
// <2=> Red 
// <3=> Green 
// <4=> Yellow 
// <5=> Blue 
// <6=> Magenta 
// <7=> Cyan 
// <8=> White 

#ifndef NRFX_TIMER_CONFIG_DEBUG_COLOR
#define NRFX_TIMER_CONFIG_DEBUG_COLOR 0
#endif

// </e>

// </e>

// <e> NRFX_TWIM_ENABLED - nrfx_twim - TWIM peripheral driver
//==========================================================
#ifndef NRFX_TWIM_ENABLED
#define NRFX_TWIM_ENABLED 0
#endif
// <q> NRFX_TWIM0_ENABLED  - Enable TWIM0 instance
 

#ifndef NRFX_TWIM0_ENABLED
#define NRFX_TWIM0_ENABLED 0
#endif

// <q> NRFX_TWIM1_ENABLED  - Enable TWIM1 instance
 

#ifndef NRFX_TWIM1_ENABLED
#define NRFX_TWIM1_ENABLED 0
#endif

// <o> NRFX_TWIM_DEFAULT_CONFIG_FREQUENCY  - Frequency
 
// <26738688=> 100k 
// <67108864=> 250k 
// <104857600=> 400k 

#ifndef NRFX_TWIM_DEFAULT_CONFIG_FREQUENCY
#define NRFX_TWIM_DEFAULT_CONFIG_FREQUENCY 26738688
#endif

// <q> NRFX_TWIM_DEFAULT_CONFIG_HOLD_BUS_UNINIT  - Enables bus holding after uninit
 

#ifndef NRFX_TWIM_DEFAULT_CONFIG_HOLD_BUS_UNINIT
#define NRFX_TWIM_DEFAULT_CONFIG_HOLD_BUS_UNINIT 0
#endif

// <o> NRFX_TWIM_DEFAULT_CONFIG_IRQ_PRIORITY  - Interrupt priority
 
// <0=> 0 (highest) 
// <1=> 1 
// <2=> 2 
// <3=> 3 
// <4=> 4 
// <5=> 5 
// <6=> 6 
// <7=> 7 

#ifndef NRFX_TWIM_DEFAULT_CONFIG_IRQ_PRIORITY
#define NRFX_TWIM_DEFAULT_CONFIG_IRQ_PRIORITY 6
#endif

// <e> NRFX_TWIM_CONFIG_LOG_ENABLED - Enables logging in the module.
//==========================================================
#ifndef NRFX_TWIM_CONFIG_LOG_ENABLED
#define NRFX_TWIM_CONFIG_LOG_ENABLED 0
#endif
// <o> NRFX_TWIM_CONFIG_LOG_LEVEL  - Default Severity level
 
// <0=> Off 
// <1=> Error 
// <2=> Warning 
// <3=> Info 
// <4=> Debug 

#ifndef NRFX_TWIM_CONFIG_LOG_LEVEL
#define NRFX_TWIM_CONFIG_LOG_LEVEL 3
#endif

// <o> NRFX_TWIM_CONFIG_INFO_COLOR  - ANSI escape code prefix.
 
// <0=> Default 
// <1=> Black 
// <2=> Red 
// <3=> Green 
// <4=> Yellow 
// <5=> Blue 
// <6=> Magenta 
// <7=> Cyan 
// <8=> White 

#ifndef NRFX_TWIM_CONFIG_INFO_COLOR
#define NRFX_TWIM_CONFIG_INFO_COLOR 0
#endif

// <o> NRFX_TWIM_CONFIG_DEBUG_COLOR  - ANSI escape code prefix.
 
// <0=> Default 
// <1=> Black 
// <2=> Red 
// <3=> Green 
// <4=> Yellow 
// <5=> Blue 
// <6=> Magenta 
// <7=> Cyan 
// <8=> White 

#ifndef NRFX_TWIM_CONFIG_DEBUG_COLOR
#define NRFX_TWIM_CONFIG_DEBUG_COLOR 0
#endif

// </e>

// </e>

// <e> NRFX_TWIS_ENABLED - nrfx_twis - TWIS peripheral driver
//==========================================================
#ifndef NRFX_TWIS_ENABLED
#define NRFX_TWIS_ENABLED 0
#endif
// <q> NRFX_TWIS0_ENABLED  - Enable TWIS0 instance
 

#ifndef NRFX_TWIS0_ENABLED
#define NRFX_TWIS0_ENABLED 0
#endif

// <q> NRFX_TWIS1_ENABLED  - Enable TWIS1 instance
 

#ifndef NRFX_TWIS1_ENABLED
#define NRFX_TWIS1_ENABLED 0
#endif

// <q> NRFX_TWIS_ASSUME_INIT_AFTER_RESET_ONLY  - Assume that any instance would be initialized only once
 

// <i> Optimization flag. Registers used by TWIS are shared by other peripherals. Normally, during initialization driver tries to clear all registers to known state before doing the initialization itself. This gives initialization safe procedure, no matter when it would be called. If you activate TWIS only once and do never uninitialize it - set this flag to 1 what gives more optimal code.

#ifndef NRFX_TWIS_ASSUME_INIT_AFTER_RESET_ONLY
#define NRFX_TWIS_ASSUME_INIT_AFTER_RESET_ONLY 0
#endif

// <q> NRFX_TWIS_NO_SYNC_MODE  - Remove support for synchronous mode
 

// <i> Synchronous mode would be used in specific situations. And it uses some additional code and data memory to safely process state machine by polling it in status functions. If this functionality is not required it may be disabled to free some resources.

#ifndef NRFX_TWIS_NO_SYNC_MODE
#define NRFX_TWIS_NO_SYNC_MODE 0
#endif

// <o> NRFX_TWIS_DEFAULT_CONFIG_ADDR0 - Address0 
#ifndef NRFX_TWIS_DEFAULT_CONFIG_ADDR0
#define NRFX_TWIS_DEFAULT_CONFIG_ADDR0 0
#endif

// <o> NRFX_TWIS_DEFAULT_CONFIG_ADDR1 - Address1 
#ifndef NRFX_TWIS_DEFAULT_CONFIG_ADDR1
#define NRFX_TWIS_DEFAULT_CONFIG_ADDR1 0
#endif

// <o> NRFX_TWIS_DEFAULT_CONFIG_SCL_PULL  - SCL pin pull configuration
 
// <0=> Disabled 
// <1=> Pull down 
// <3=> Pull up 

#ifndef NRFX_TWIS_DEFAULT_CONFIG_SCL_PULL
#define NRFX_TWIS_DEFAULT_CONFIG_SCL_PULL 0
#endif

// <o> NRFX_TWIS_DEFAULT_CONFIG_SDA_PULL  - SDA pin pull configuration
 
// <0=> Disabled 
// <1=> Pull down 
// <3=> Pull up 

#ifndef NRFX_TWIS_DEFAULT_CONFIG_SDA_PULL
#define NRFX_TWIS_DEFAULT_CONFIG_SDA_PULL 0
#endif

// <o> NRFX_TWIS_DEFAULT_CONFIG_IRQ_PRIORITY  - Interrupt priority
 
// <0=> 0 (highest) 
// <1=> 1 
// <2=> 2 
// <3=> 3 
// <4=> 4 
// <5=> 5 
// <6=> 6 
// <7=> 7 

#ifndef NRFX_TWIS_DEFAULT_CONFIG_IRQ_PRIORITY
#define NRFX_TWIS_DEFAULT_CONFIG_IRQ_PRIORITY 6
#endif

// <e> NRFX_TWIS_CONFIG_LOG_ENABLED - Enables logging in the module.
//==========================================================
#ifndef NRFX_TWIS_CONFIG_LOG_ENABLED
#define NRFX_TWIS_CONFIG_LOG_ENABLED 0
#endif
// <o> NRFX_TWIS_CONFIG_LOG_LEVEL  - Default Severity level
 
// <0=> Off 
// <1=> Error 
// <2=> Warning 
// <3=> Info 
// <4=> Debug 

#ifndef NRFX_TWIS_CONFIG_LOG_LEVEL
#define NRFX_TWIS_CONFIG_LOG_LEVEL 3
#endif

// <o> NRFX_TWIS_CONFIG_INFO_COLOR  - ANSI escape code prefix.
 
// <0=> Default 
// <1=> Black 
// <2=> Red 
// <3=> Green 
// <4=> Yellow 
// <5=> Blue 
// <6=> Magenta 
// <7=> Cyan 
// <8=> White 

#ifndef NRFX_TWIS_CONFIG_INFO_COLOR
#define NRFX_TWIS_CONFIG_INFO_COLOR 0
#endif

// <o> NRFX_TWIS_CONFIG_DEBUG_COLOR  - ANSI escape code prefix.
 
// <0=> Default 
// <1=> Black 
// <2=> Red 
// <3=> Green 
// <4=> Yellow 
// <5=> Blue 
// <6=> Magenta 
// <7=> Cyan 
// <8=> White 

#ifndef NRFX_TWIS_CONFIG_DEBUG_COLOR
#define NRFX_TWIS_CONFIG_DEBUG_COLOR 0
#endif

// </e>

// </e>

// <e> NRFX_TWI_ENABLED - nrfx_twi - TWI peripheral driver
//==========================================================
#ifndef NRFX_TWI_ENABLED
#define NRFX_TWI_ENABLED 0
#endif
// <q> NRFX_TWI0_ENABLED  - Enable TWI0 instance
 

#ifndef NRFX_TWI0_ENABLED
#define NRFX_TWI0_ENABLED 0
#endif

// <q> NRFX_TWI1_ENABLED  - Enable TWI1 instance
 

#ifndef NRFX_TWI1_ENABLED
#define NRFX_TWI1_ENABLED 0
#endif

// <o> NRFX_TWI_DEFAULT_CONFIG_FREQUENCY  - Frequency
 
// <26738688=> 100k 
// <67108864=> 250k 
// <104857600=> 400k 

#ifndef NRFX_TWI_DEFAULT_CONFIG_FREQUENCY
#define NRFX_TWI_DEFAULT_CONFIG_FREQUENCY 26738688
#endif

// <q> NRFX_TWI_DEFAULT_CONFIG_HOLD_BUS_UNINIT  - Enables bus holding after uninit
 

#ifndef NRFX_TWI_DEFAULT_CONFIG_HOLD_BUS_UNINIT
#define NRFX_TWI_DEFAULT_CONFIG_HOLD_BUS_UNINIT 0
#endif

// <o> NRFX_TWI_DEFAULT_CONFIG_IRQ_PRIORITY  - Interrupt priority
 
// <0=> 0 (highest) 
// <1=> 1 
// <2=> 2 
// <3=> 3 
// <4=> 4 
// <5=> 5 
// <6=> 6 
// <7=> 7 

#ifndef NRFX_TWI_DEFAULT_CONFIG_IRQ_PRIORITY
#define NRFX_TWI_DEFAULT_CONFIG_IRQ_PRIORITY 6
#endif

// <e> NRFX_TWI_CONFIG_LOG_ENABLED - Enables logging in the module.
//==========================================================
#ifndef NRFX_TWI_CONFIG_LOG_ENABLED
#define NRFX_TWI_CONFIG_LOG_ENABLED 0
#endif
// <o> NRFX_TWI_CONFIG_LOG_LEVEL  - Default Severity level
 
// <0=> Off 
// <1=> Error 
// <2=> Warning 
// <3=> Info 
// <4=> Debug 

#ifndef NRFX_TWI_CONFIG_LOG_LEVEL
#define NRFX_TWI_CONFIG_LOG_LEVEL 3
#endif

// <o> NRFX_TWI_CONFIG_INFO_COLOR  - ANSI escape code prefix.
 
// <0=> Default 
// <1=> Black 
// <2=> Red 
// <3=> Green 
// <4=> Yellow 
// <5=> Blue 
// <6=> Magenta 
// <7=> Cyan 
// <8=> White 

#ifndef NRFX_TWI_CONFIG_INFO_COLOR
#define NRFX_TWI_CONFIG_INFO_COLOR 0
#endif

// <o> NRFX_TWI_CONFIG_DEBUG_COLOR  - ANSI escape code prefix.
 
// <0=> Default 
// <1=> Black 
// <2=> Red 
// <3=> Green 
// <4=> Yellow 
// <5=> Blue 
// <6=> Magenta 
// <7=> Cyan 
// <8=> White 

#ifndef NRFX_TWI_CONFIG_DEBUG_COLOR
#define NRFX_TWI_CONFIG_DEBUG_COLOR 0
#endif

// </e>

// </e>

// <e> NRFX_UARTE_ENABLED - nrfx_uarte - UARTE peripheral driver
//==========================================================
#ifndef NRFX_UARTE_ENABLED
#define NRFX_UARTE_ENABLED 1
#endif
// <o> NRFX_UARTE0_ENABLED - Enable UARTE0 instance 
#ifndef NRFX_UARTE0_ENABLED
#define NRFX_UARTE0_ENABLED 0
#endif

// <o> NRFX_UARTE1_ENABLED - Enable UARTE1 instance 
#ifndef NRFX_UARTE1_ENABLED
#define NRFX_UARTE1_ENABLED 0
#endif

// <o> NRFX_UARTE_DEFAULT_CONFIG_HWFC  - Hardware Flow Control
 
// <0=> Disabled 
// <1=> Enabled 

#ifndef NRFX_UARTE_DEFAULT_CONFIG_HWFC
#define NRFX_UARTE_DEFAULT_CONFIG_HWFC 0
#endif

// <o> NRFX_UARTE_DEFAULT_CONFIG_PARITY  - Parity
 
// <0=> Excluded 
// <14=> Included 

#ifndef NRFX_UARTE_DEFAULT_CONFIG_PARITY
#define NRFX_UARTE_DEFAULT_CONFIG_PARITY 0
#endif

// <o> NRFX_UARTE_DEFAULT_CONFIG_BAUDRATE  - Default Baudrate
 
// <323584=> 1200 baud 
// <643072=> 2400 baud 
// <1290240=> 4800 baud 
// <2576384=> 9600 baud 
// <3862528=> 14400 baud 
// <5152768=> 19200 baud 
// <7716864=> 28800 baud 
// <8388608=> 31250 baud 
// <10289152=> 38400 baud 
// <15007744=> 56000 baud 
// <15400960=> 57600 baud 
// <20615168=> 76800 baud 
// <30801920=> 115200 baud 
// <61865984=> 230400 baud 
// <67108864=> 250000 baud 
// <121634816=> 460800 baud 
// <251658240=> 921600 baud 
// <268435456=> 1000000 baud 

#ifndef NRFX_UARTE_DEFAULT_CONFIG_BAUDRATE
#define NRFX_UARTE_DEFAULT_CONFIG_BAUDRATE 30801920
#endif

// <o> NRFX_UARTE_DEFAULT_CONFIG_IRQ_PRIORITY  - Interrupt priority
 
// <0=> 0 (highest) 
// <1=> 1 
// <2=> 2 
// <3=> 3 
// <4=> 4 
// <5=> 5 
// <6=> 6 
// <7=> 7 

#ifndef NRFX_UARTE_DEFAULT_CONFIG_IRQ_PRIORITY
#define NRFX_UARTE_DEFAULT_CONFIG_IRQ_PRIORITY 6
#endif

// <e> NRFX_UARTE_CONFIG_LOG_ENABLED - Enables logging in the module.
//==========================================================
#ifndef NRFX_UARTE_CONFIG_LOG_ENABLED
#define NRFX_UARTE_CONFIG_LOG_ENABLED 0
#endif
// <o> NRFX_UARTE_CONFIG_LOG_LEVEL  - Default Severity level
 
// <0=> Off 
// <1=> Error 
// <2=> Warning 
// <3=> Info 
// <4=> Debug 

#ifndef NRFX_UARTE_CONFIG_LOG_LEVEL
#define NRFX_UARTE_CONFIG_LOG_LEVEL 3
#endif

// <o> NRFX_UARTE_CONFIG_INFO_COLOR  - ANSI escape code prefix.
 
// <0=> Default 
// <1=> Black 
// <2=> Red 
// <3=> Green 
// <4=> Yellow 
// <5=> Blue 
// <6=> Magenta 
// <7=> Cyan 
// <8=> White 

#ifndef NRFX_UARTE_CONFIG_INFO_COLOR
#define NRFX_UARTE_CONFIG_INFO_COLOR 0
#endif

// <o> NRFX_UARTE_CONFIG_DEBUG_COLOR  - ANSI escape code prefix.
 
// <0=> Default 
// <1=> Black 
// <2=> Red 
// <3=> Green 
// <4=> Yellow 
// <5=> Blue 
// <6=> Magenta 
// <7=> Cyan 
// <8=> White 

#ifndef NRFX_UARTE_CONFIG_DEBUG_COLOR
#define NRFX_UARTE_CONFIG_DEBUG_COLOR 0
#endif

// </e>

// </e>

// <e> NRFX_UART_ENABLED - nrfx_uart - UART peripheral driver
//==========================================================
#ifndef NRFX_UART_ENABLED
#define NRFX_UART_ENABLED 1
#endif
// <o> NRFX_UART0_ENABLED - Enable UART0 instance 
#ifndef NRFX_UART0_ENABLED
#define NRFX_UART0_ENABLED 0
#endif

// <o> NRFX_UART_DEFAULT_CONFIG_HWFC  - Hardware Flow Control
 
// <0=> Disabled 
// <1=> Enabled 

#ifndef NRFX_UART_DEFAULT_CONFIG_HWFC
#define NRFX_UART_DEFAULT_CONFIG_HWFC 0
#endif

// <o> NRFX_UART_DEFAULT_CONFIG_PARITY  - Parity
 
// <0=> Excluded 
// <14=> Included 

#ifndef NRFX_UART_DEFAULT_CONFIG_PARITY
#define NRFX_UART_DEFAULT_CONFIG_PARITY 0
#endif

// <o> NRFX_UART_DEFAULT_CONFIG_BAUDRATE  - Default Baudrate
 
// <323584=> 1200 baud 
// <643072=> 2400 baud 
// <1290240=> 4800 baud 
// <2576384=> 9600 baud 
// <3866624=> 14400 baud 
// <5152768=> 19200 baud 
// <7729152=> 28800 baud 
// <8388608=> 31250 baud 
// <10309632=> 38400 baud 
// <15007744=> 56000 baud 
// <15462400=> 57600 baud 
// <20615168=> 76800 baud 
// <30924800=> 115200 baud 
// <61845504=> 230400 baud 
// <67108864=> 250000 baud 
// <123695104=> 460800 baud 
// <247386112=> 921600 baud 
// <268435456=> 1000000 baud 

#ifndef NRFX_UART_DEFAULT_CONFIG_BAUDRATE
#define NRFX_UART_DEFAULT_CONFIG_BAUDRATE 30924800
#endif

// <o> NRFX_UART_DEFAULT_CONFIG_IRQ_PRIORITY  - Interrupt priority
 
// <0=> 0 (highest) 
// <1=> 1 
// <2=> 2 
// <3=> 3 
// <4=> 4 
// <5=> 5 
// <6=> 6 
// <7=> 7 

#ifndef NRFX_UART_DEFAULT_CONFIG_IRQ_PRIORITY
#define NRFX_UART_DEFAULT_CONFIG_IRQ_PRIORITY 6
#endif

// <e> NRFX_UART_CONFIG_LOG_ENABLED - Enables logging in the module.
//==========================================================
#ifndef NRFX_UART_CONFIG_LOG_ENABLED
#define NRFX_UART_CONFIG_LOG_ENABLED 0
#endif
// <o> NRFX_UART_CONFIG_LOG_LEVEL  - Default Severity level
 
// <0=> Off 
// <1=> Error 
// <2=> Warning 
// <3=> Info 
// <4=> Debug 

#ifndef NRFX_UART_CONFIG_LOG_LEVEL
#define NRFX_UART_CONFIG_LOG_LEVEL 3
#endif

// <o> NRFX_UART_CONFIG_INFO_COLOR  - ANSI escape code prefix.
 
// <0=> Default 
// <1=> Black 
// <2=> Red 
// <3=> Green 
// <4=> Yellow 
// <5=> Blue 
// <6=> Magenta 
// <7=> Cyan 
// <8=> White 

#ifndef NRFX_UART_CONFIG_INFO_COLOR
#define NRFX_UART_CONFIG_INFO_COLOR 0
#endif

// <o> NRFX_UART_CONFIG_DEBUG_COLOR  - ANSI escape code prefix.
 
// <0=> Default 
// <1=> Black 
// <2=> Red 
// <3=> Green 
// <4=> Yellow 
// <5=> Blue 
// <6=> Magenta 
// <7=> Cyan 
// <8=> White 

#ifndef NRFX_UART_CONFIG_DEBUG_COLOR
#define NRFX_UART_CONFIG_DEBUG_COLOR 0
#endif

// </e>

// </e>

// <e> NRFX_USBD_ENABLED - nrfx_usbd - USBD peripheral driver
//==========================================================
#ifndef NRFX_USBD_ENABLED
#define NRFX_USBD_ENABLED 0
#endif
// <o> NRFX_USBD_CONFIG_IRQ_PRIORITY  - Interrupt priority
 
// <0=> 0 (highest) 
// <1=> 1 
// <2=> 2 
// <3=> 3 
// <4=> 4 
// <5=> 5 
// <6=> 6 
// <7=> 7 

#ifndef NRFX_USBD_CONFIG_IRQ_PRIORITY
#define NRFX_USBD_CONFIG_IRQ_PRIORITY 6
#endif

// <o> NRFX_USBD_CONFIG_DMASCHEDULER_MODE  - USBD DMA scheduler working scheme
 
// <0=> Prioritized access 
// <1=> Round Robin 

#ifndef NRFX_USBD_CONFIG_DMASCHEDULER_MODE
#define NRFX_USBD_CONFIG_DMASCHEDULER_MODE 0
#endif

// <q> NRFX_USBD_CONFIG_DMASCHEDULER_ISO_BOOST  - Give priority to isochronous transfers
 

// <i> This option gives priority to isochronous transfers.
// <i> Enabling it assures that isochronous transfers are always processed,
// <i> even if multiple other transfers are pending.
// <i> Isochronous endpoints are prioritized before the usbd_dma_scheduler_algorithm
// <i> function is called, so the option is independent of the algorithm chosen.

#ifndef NRFX_USBD_CONFIG_DMASCHEDULER_ISO_BOOST
#define NRFX_USBD_CONFIG_DMASCHEDULER_ISO_BOOST 1
#endif

// <q> NRFX_USBD_CONFIG_ISO_IN_ZLP  - Respond to an IN token on ISO IN endpoint with ZLP when no data is ready
 

// <i> If set, ISO IN endpoint will respond to an IN token with ZLP when no data is ready to be sent.
// <i> Else, there will be no response.

#ifndef NRFX_USBD_CONFIG_ISO_IN_ZLP
#define NRFX_USBD_CONFIG_ISO_IN_ZLP 0
#endif

// <q> NRFX_USBD_USE_WORKAROUND_FOR_ANOMALY_211  - Use workaround for anomaly 211
 

// <i> If set, workaround for anomaly 211 will be enabled.
// <i> Anomaly 211 - Device remains in SUSPEND too long when host resumes
// <i> bus activity (sending SOF packets) without a RESUME condition.

#ifndef NRFX_USBD_USE_WORKAROUND_FOR_ANOMALY_211
#define NRFX_USBD_USE_WORKAROUND_FOR_ANOMALY_211 0
#endif

// </e>

// <e> NRFX_WDT_ENABLED - nrfx_wdt - WDT peripheral driver
//==========================================================
#ifndef NRFX_WDT_ENABLED
#define NRFX_WDT_ENABLED 0
#endif
// <o> NRFX_WDT_CONFIG_BEHAVIOUR  - WDT behavior in CPU SLEEP or HALT mode
 
// <1=> Run in SLEEP, Pause in HALT 
// <8=> Pause in SLEEP, Run in HALT 
// <9=> Run in SLEEP and HALT 
// <0=> Pause in SLEEP and HALT 

#ifndef NRFX_WDT_CONFIG_BEHAVIOUR
#define NRFX_WDT_CONFIG_BEHAVIOUR 1
#endif

// <o> NRFX_WDT_CONFIG_RELOAD_VALUE - Reload value in ms  <1-131072000> 


#ifndef NRFX_WDT_CONFIG_RELOAD_VALUE
#define NRFX_WDT_CONFIG_RELOAD_VALUE 2000
#endif

// <o> NRFX_WDT_CONFIG_NO_IRQ  - Remove WDT IRQ handling from WDT driver
 
// <0=> Include WDT IRQ handling 
// <1=> Remove WDT IRQ handling 

#ifndef NRFX_WDT_CONFIG_NO_IRQ
#define NRFX_WDT_CONFIG_NO_IRQ 0
#endif

// <o> NRFX_WDT_CONFIG_IRQ_PRIORITY  - Interrupt priority
 
// <0=> 0 (highest) 
// <1=> 1 
// <2=> 2 
// <3=> 3 
// <4=> 4 
// <5=> 5 
// <6=> 6 
// <7=> 7 

#ifndef NRFX_WDT_CONFIG_IRQ_PRIORITY
#define NRFX_WDT_CONFIG_IRQ_PRIORITY 6
#endif

// <e> NRFX_WDT_CONFIG_LOG_ENABLED - Enables logging in the module.
//==========================================================
#ifndef NRFX_WDT_CONFIG_LOG_ENABLED
#define NRFX_WDT_CONFIG_LOG_ENABLED 0
#endif
// <o> NRFX_WDT_CONFIG_LOG_LEVEL  - Default Severity level
 
// <0=> Off 
// <1=> Error 
// <2=> Warning 
// <3=> Info 
// <4=> Debug 

#ifndef NRFX_WDT_CONFIG_LOG_LEVEL
#define NRFX_WDT_CONFIG_LOG_LEVEL 3
#endif

// <o> NRFX_WDT_CONFIG_INFO_COLOR  - ANSI escape code prefix.
 
// <0=> Default 
// <1=> Black 
// <2=> Red 
// <3=> Green 
// <4=> Yellow 
// <5=> Blue 
// <6=> Magenta 
// <7=> Cyan 
// <8=> White 

#ifndef NRFX_WDT_CONFIG_INFO_COLOR
#define NRFX_WDT_CONFIG_INFO_COLOR 0
#endif

// <o> NRFX_WDT_CONFIG_DEBUG_COLOR  - ANSI escape code prefix.
 
// <0=> Default 
// <1=> Black 
// <2=> Red 
// <3=> Green 
// <4=> Yellow 
// <5=> Blue 
// <6=> Magenta 
// <7=> Cyan 
// <8=> White 

#ifndef NRFX_WDT_CONFIG_DEBUG_COLOR
#define NRFX_WDT_CONFIG_DEBUG_COLOR 0
#endif

// </e>

// </e>

// <e> NRF_CLOCK_ENABLED - nrf_drv_clock - CLOCK peripheral driver - legacy layer
//==========================================================
#ifndef NRF_CLOCK_ENABLED
#define NRF_CLOCK_ENABLED 1
#endif
// <o> CLOCK_CONFIG_LF_SRC  - LF Clock Source
 
// <0=> RC 
// <1=> XTAL 
// <2=> Synth 
// <131073=> External Low Swing 
// <196609=> External Full Swing 

#ifndef CLOCK_CONFIG_LF_SRC
#define CLOCK_CONFIG_LF_SRC 1
#endif

// <q> CLOCK_CONFIG_LF_CAL_ENABLED  - Calibration enable for LF Clock Source
 

#ifndef CLOCK_CONFIG_LF_CAL_ENABLED
#define CLOCK_CONFIG_LF_CAL_ENABLED 0
#endif

// <o> CLOCK_CONFIG_IRQ_PRIORITY  - Interrupt priority
 

// <i> Priorities 0,2 (nRF51) and 0,1,4,5 (nRF52) are reserved for SoftDevice
// <0=> 0 (highest) 
// <1=> 1 
// <2=> 2 
// <3=> 3 
// <4=> 4 
// <5=> 5 
// <6=> 6 
// <7=> 7 

#ifndef CLOCK_CONFIG_IRQ_PRIORITY
#define CLOCK_CONFIG_IRQ_PRIORITY 6
#endif

// </e>

// <e> PDM_ENABLED - nrf_drv_pdm - PDM peripheral driver - legacy layer
//==========================================================
#ifndef PDM_ENABLED
#define PDM_ENABLED 0
#endif
// <o> PDM_CONFIG_MODE  - Mode
 
// <0=> Stereo 
// <1=> Mono 

#ifndef PDM_CONFIG_MODE
#define PDM_CONFIG_MODE 1
#endif

// <o> PDM_CONFIG_EDGE  - Edge
 
// <0=> Left falling 
// <1=> Left rising 

#ifndef PDM_CONFIG_EDGE
#define PDM_CONFIG_EDGE 0
#endif

// <o> PDM_CONFIG_CLOCK_FREQ  - Clock frequency
 
// <134217728=> 1000k 
// <138412032=> 1032k (default) 
// <142606336=> 1067k 

#ifndef PDM_CONFIG_CLOCK_FREQ
#define PDM_CONFIG_CLOCK_FREQ 138412032
#endif

// <o> PDM_CONFIG_IRQ_PRIORITY  - Interrupt priority
 

// <i> Priorities 0,2 (nRF51) and 0,1,4,5 (nRF52) are reserved for SoftDevice
// <0=> 0 (highest) 
// <1=> 1 
// <2=> 2 
// <3=> 3 
// <4=> 4 
// <5=> 5 
// <6=> 6 
// <7=> 7 

#ifndef PDM_CONFIG_IRQ_PRIORITY
#define PDM_CONFIG_IRQ_PRIORITY 6
#endif

// </e>

// <e> POWER_ENABLED - nrf_drv_power - POWER peripheral driver - legacy layer
//==========================================================
#ifndef POWER_ENABLED
#define POWER_ENABLED 0
#endif
// <o> POWER_CONFIG_IRQ_PRIORITY  - Interrupt priority
 

// <i> Priorities 0,2 (nRF51) and 0,1,4,5 (nRF52) are reserved for SoftDevice
// <0=> 0 (highest) 
// <1=> 1 
// <2=> 2 
// <3=> 3 
// <4=> 4 
// <5=> 5 
// <6=> 6 
// <7=> 7 

#ifndef POWER_CONFIG_IRQ_PRIORITY
#define POWER_CONFIG_IRQ_PRIORITY 6
#endif

// <q> POWER_CONFIG_DEFAULT_DCDCEN  - The default configuration of main DCDC regulator
 

// <i> This settings means only that components for DCDC regulator are installed and it can be enabled.

#ifndef POWER_CONFIG_DEFAULT_DCDCEN
#define POWER_CONFIG_DEFAULT_DCDCEN 0
#endif

// <q> POWER_CONFIG_DEFAULT_DCDCENHV  - The default configuration of High Voltage DCDC regulator
 

// <i> This settings means only that components for DCDC regulator are installed and it can be enabled.

#ifndef POWER_CONFIG_DEFAULT_DCDCENHV
#define POWER_CONFIG_DEFAULT_DCDCENHV 0
#endif

// </e>

// <q> PPI_ENABLED  - nrf_drv_ppi - PPI peripheral driver - legacy layer
 

#ifndef PPI_ENABLED
#define PPI_ENABLED 0
#endif

// <e> PWM_ENABLED - nrf_drv_pwm - PWM peripheral driver - legacy layer
//==========================================================
#ifndef PWM_ENABLED
#define PWM_ENABLED 0
#endif
// <o> PWM_DEFAULT_CONFIG_OUT0_PIN - Out0 pin  <0-31> 


#ifndef PWM_DEFAULT_CONFIG_OUT0_PIN
#define PWM_DEFAULT_CONFIG_OUT0_PIN 31
#endif

// <o> PWM_DEFAULT_CONFIG_OUT1_PIN - Out1 pin  <0-31> 


#ifndef PWM_DEFAULT_CONFIG_OUT1_PIN
#define PWM_DEFAULT_CONFIG_OUT1_PIN 31
#endif

// <o> PWM_DEFAULT_CONFIG_OUT2_PIN - Out2 pin  <0-31> 


#ifndef PWM_DEFAULT_CONFIG_OUT2_PIN
#define PWM_DEFAULT_CONFIG_OUT2_PIN 31
#endif

// <o> PWM_DEFAULT_CONFIG_OUT3_PIN - Out3 pin  <0-31> 


#ifndef PWM_DEFAULT_CONFIG_OUT3_PIN
#define PWM_DEFAULT_CONFIG_OUT3_PIN 31
#endif

// <o> PWM_DEFAULT_CONFIG_BASE_CLOCK  - Base clock
 
// <0=> 16 MHz 
// <1=> 8 MHz 
// <2=> 4 MHz 
// <3=> 2 MHz 
// <4=> 1 MHz 
// <5=> 500 kHz 
// <6=> 250 kHz 
// <7=> 125 kHz 

#ifndef PWM_DEFAULT_CONFIG_BASE_CLOCK
#define PWM_DEFAULT_CONFIG_BASE_CLOCK 4
#endif

// <o> PWM_DEFAULT_CONFIG_COUNT_MODE  - Count mode
 
// <0=> Up 
// <1=> Up and Down 

#ifndef PWM_DEFAULT_CONFIG_COUNT_MODE
#define PWM_DEFAULT_CONFIG_COUNT_MODE 0
#endif

// <o> PWM_DEFAULT_CONFIG_TOP_VALUE - Top value 
#ifndef PWM_DEFAULT_CONFIG_TOP_VALUE
#define PWM_DEFAULT_CONFIG_TOP_VALUE 1000
#endif

// <o> PWM_DEFAULT_CONFIG_LOAD_MODE  - Load mode
 
// <0=> Common 
// <1=> Grouped 
// <2=> Individual 
// <3=> Waveform 

#ifndef PWM_DEFAULT_CONFIG_LOAD_MODE
#define PWM_DEFAULT_CONFIG_LOAD_MODE 0
#endif

// <o> PWM_DEFAULT_CONFIG_STEP_MODE  - Step mode
 
// <0=> Auto 
// <1=> Triggered 

#ifndef PWM_DEFAULT_CONFIG_STEP_MODE
#define PWM_DEFAULT_CONFIG_STEP_MODE 0
#endif

// <o> PWM_DEFAULT_CONFIG_IRQ_PRIORITY  - Interrupt priority
 

// <i> Priorities 0,2 (nRF51) and 0,1,4,5 (nRF52) are reserved for SoftDevice
// <0=> 0 (highest) 
// <1=> 1 
// <2=> 2 
// <3=> 3 
// <4=> 4 
// <5=> 5 
// <6=> 6 
// <7=> 7 

#ifndef PWM_DEFAULT_CONFIG_IRQ_PRIORITY
#define PWM_DEFAULT_CONFIG_IRQ_PRIORITY 6
#endif

// <q> PWM0_ENABLED  - Enable PWM0 instance
 

#ifndef PWM0_ENABLED
#define PWM0_ENABLED 0
#endif

// <q> PWM1_ENABLED  - Enable PWM1 instance
 

#ifndef PWM1_ENABLED
#define PWM1_ENABLED 0
#endif

// <q> PWM2_ENABLED  - Enable PWM2 instance
 

#ifndef PWM2_ENABLED
#define PWM2_ENABLED 0
#endif

// <q> PWM3_ENABLED  - Enable PWM3 instance
 

#ifndef PWM3_ENABLED
#define PWM3_ENABLED 0
#endif

// </e>

// <e> QDEC_ENABLED - nrf_drv_qdec - QDEC peripheral driver - legacy layer
//==========================================================
#ifndef QDEC_ENABLED
#define QDEC_ENABLED 0
#endif
// <o> QDEC_CONFIG_REPORTPER  - Report period
 
// <0=> 10 Samples 
// <1=> 40 Samples 
// <2=> 80 Samples 
// <3=> 120 Samples 
// <4=> 160 Samples 
// <5=> 200 Samples 
// <6=> 240 Samples 
// <7=> 280 Samples 

#ifndef QDEC_CONFIG_REPORTPER
#define QDEC_CONFIG_REPORTPER 0
#endif

// <o> QDEC_CONFIG_SAMPLEPER  - Sample period
 
// <0=> 128 us 
// <1=> 256 us 
// <2=> 512 us 
// <3=> 1024 us 
// <4=> 2048 us 
// <5=> 4096 us 
// <6=> 8192 us 
// <7=> 16384 us 

#ifndef QDEC_CONFIG_SAMPLEPER
#define QDEC_CONFIG_SAMPLEPER 7
#endif

// <o> QDEC_CONFIG_PIO_A - A pin  <0-31> 


#ifndef QDEC_CONFIG_PIO_A
#define QDEC_CONFIG_PIO_A 31
#endif

// <o> QDEC_CONFIG_PIO_B - B pin  <0-31> 


#ifndef QDEC_CONFIG_PIO_B
#define QDEC_CONFIG_PIO_B 31
#endif

// <o> QDEC_CONFIG_PIO_LED - LED pin  <0-31> 


#ifndef QDEC_CONFIG_PIO_LED
#define QDEC_CONFIG_PIO_LED 31
#endif

// <o> QDEC_CONFIG_LEDPRE - LED pre 
#ifndef QDEC_CONFIG_LEDPRE
#define QDEC_CONFIG_LEDPRE 511
#endif

// <o> QDEC_CONFIG_LEDPOL  - LED polarity
 
// <0=> Active low 
// <1=> Active high 

#ifndef QDEC_CONFIG_LEDPOL
#define QDEC_CONFIG_LEDPOL 1
#endif

// <q> QDEC_CONFIG_DBFEN  - Debouncing enable
 

#ifndef QDEC_CONFIG_DBFEN
#define QDEC_CONFIG_DBFEN 0
#endif

// <q> QDEC_CONFIG_SAMPLE_INTEN  - Sample ready interrupt enable
 

#ifndef QDEC_CONFIG_SAMPLE_INTEN
#define QDEC_CONFIG_SAMPLE_INTEN 0
#endif

// <o> QDEC_CONFIG_IRQ_PRIORITY  - Interrupt priority
 

// <i> Priorities 0,2 (nRF51) and 0,1,4,5 (nRF52) are reserved for SoftDevice
// <0=> 0 (highest) 
// <1=> 1 
// <2=> 2 
// <3=> 3 
// <4=> 4 
// <5=> 5 
// <6=> 6 
// <7=> 7 

#ifndef QDEC_CONFIG_IRQ_PRIORITY
#define QDEC_CONFIG_IRQ_PRIORITY 6
#endif

// </e>

// <e> QSPI_ENABLED - nrf_drv_qspi - QSPI peripheral driver - legacy layer
//==========================================================
#ifndef QSPI_ENABLED
#define QSPI_ENABLED 0
#endif
// <o> QSPI_CONFIG_SCK_DELAY - tSHSL, tWHSL and tSHWL in number of 16 MHz periods (62.5 ns).  <0-255> 


#ifndef QSPI_CONFIG_SCK_DELAY
#define QSPI_CONFIG_SCK_DELAY 1
#endif

// <o> QSPI_CONFIG_XIP_OFFSET - Address offset in the external memory for Execute in Place operation. 
#ifndef QSPI_CONFIG_XIP_OFFSET
#define QSPI_CONFIG_XIP_OFFSET 0
#endif

// <o> QSPI_CONFIG_READOC  - Number of data lines and opcode used for reading.
 
// <0=> FastRead 
// <1=> Read2O 
// <2=> Read2IO 
// <3=> Read4O 
// <4=> Read4IO 

#ifndef QSPI_CONFIG_READOC
#define QSPI_CONFIG_READOC 0
#endif

// <o> QSPI_CONFIG_WRITEOC  - Number of data lines and opcode used for writing.
 
// <0=> PP 
// <1=> PP2O 
// <2=> PP4O 
// <3=> PP4IO 

#ifndef QSPI_CONFIG_WRITEOC
#define QSPI_CONFIG_WRITEOC 0
#endif

// <o> QSPI_CONFIG_ADDRMODE  - Addressing mode.
 
// <0=> 24bit 
// <1=> 32bit 

#ifndef QSPI_CONFIG_ADDRMODE
#define QSPI_CONFIG_ADDRMODE 0
#endif

// <o> QSPI_CONFIG_MODE  - SPI mode.
 
// <0=> Mode 0 
// <1=> Mode 1 

#ifndef QSPI_CONFIG_MODE
#define QSPI_CONFIG_MODE 0
#endif

// <o> QSPI_CONFIG_FREQUENCY  - Frequency divider.
 
// <0=> 32MHz/1 
// <1=> 32MHz/2 
// <2=> 32MHz/3 
// <3=> 32MHz/4 
// <4=> 32MHz/5 
// <5=> 32MHz/6 
// <6=> 32MHz/7 
// <7=> 32MHz/8 
// <8=> 32MHz/9 
// <9=> 32MHz/10 
// <10=> 32MHz/11 
// <11=> 32MHz/12 
// <12=> 32MHz/13 
// <13=> 32MHz/14 
// <14=> 32MHz/15 
// <15=> 32MHz/16 

#ifndef QSPI_CONFIG_FREQUENCY
#define QSPI_CONFIG_FREQUENCY 15
#endif

// <s> QSPI_PIN_SCK - SCK pin value.
#ifndef QSPI_PIN_SCK
#define QSPI_PIN_SCK NRF_QSPI_PIN_NOT_CONNECTED
#endif

// <s> QSPI_PIN_CSN - CSN pin value.
#ifndef QSPI_PIN_CSN
#define QSPI_PIN_CSN NRF_QSPI_PIN_NOT_CONNECTED
#endif

// <s> QSPI_PIN_IO0 - IO0 pin value.
#ifndef QSPI_PIN_IO0
#define QSPI_PIN_IO0 NRF_QSPI_PIN_NOT_CONNECTED
#endif

// <s> QSPI_PIN_IO1 - IO1 pin value.
#ifndef QSPI_PIN_IO1
#define QSPI_PIN_IO1 NRF_QSPI_PIN_NOT_CONNECTED
#endif

// <s> QSPI_PIN_IO2 - IO2 pin value.
#ifndef QSPI_PIN_IO2
#define QSPI_PIN_IO2 NRF_QSPI_PIN_NOT_CONNECTED
#endif

// <s> QSPI_PIN_IO3 - IO3 pin value.
#ifndef QSPI_PIN_IO3
#define QSPI_PIN_IO3 NRF_QSPI_PIN_NOT_CONNECTED
#endif

// <o> QSPI_CONFIG_IRQ_PRIORITY  - Interrupt priority
 

// <i> Priorities 0,2 (nRF51) and 0,1,4,5 (nRF52) are reserved for SoftDevice
// <0=> 0 (highest) 
// <1=> 1 
// <2=> 2 
// <3=> 3 
// <4=> 4 
// <5=> 5 
// <6=> 6 
// <7=> 7
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
